HidetoNiwa/one-person-catch-robo/CAD/ロボット/Images/ロボット.iam 構造解析レポート 2020_07_17/0/Constraint_0_1.png

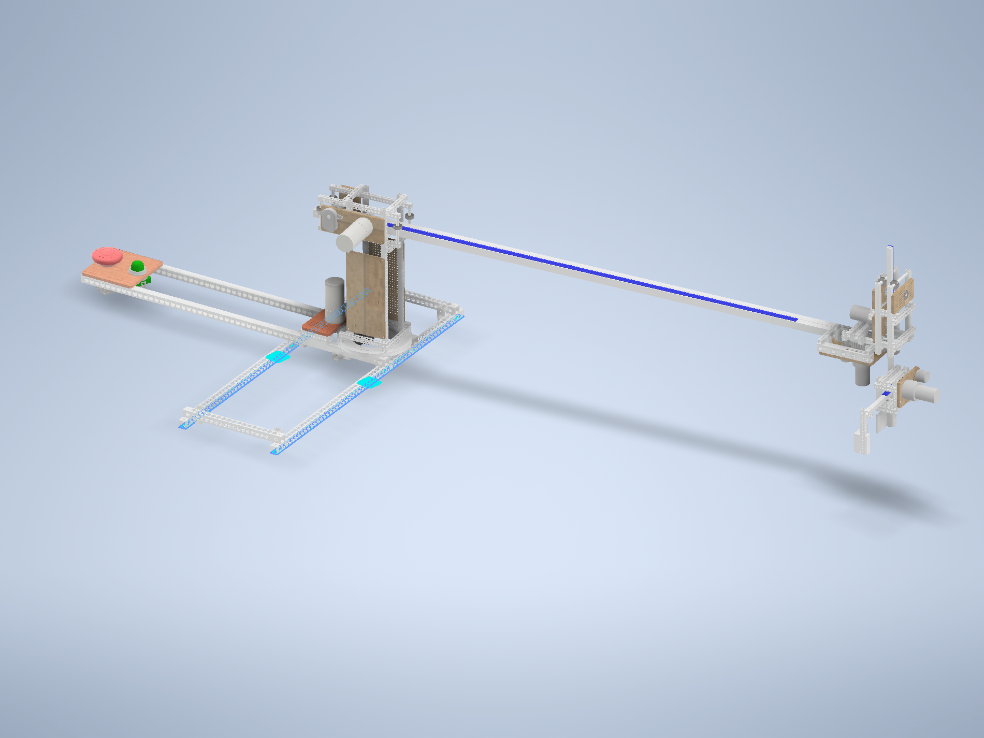
CAD/ロボット/Images/ロボット.iam 構造解析レポート 2020_07_17/0/Constraint_0_1.png
