HidetoNiwa/one-person-catch-robo/CAD/ロボット/ハンド/ハンド.png

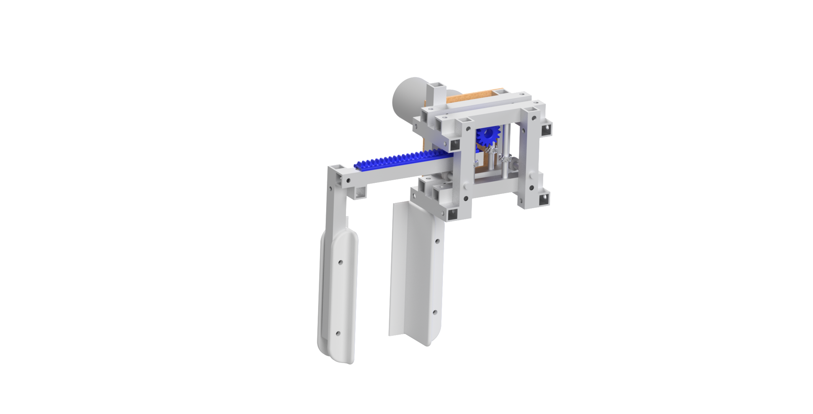
CAD/ロボット/ハンド/ハンド.png
