HidetoNiwa/one-person-catch-robo/CAD/ロボット/画像/ハンド2.png

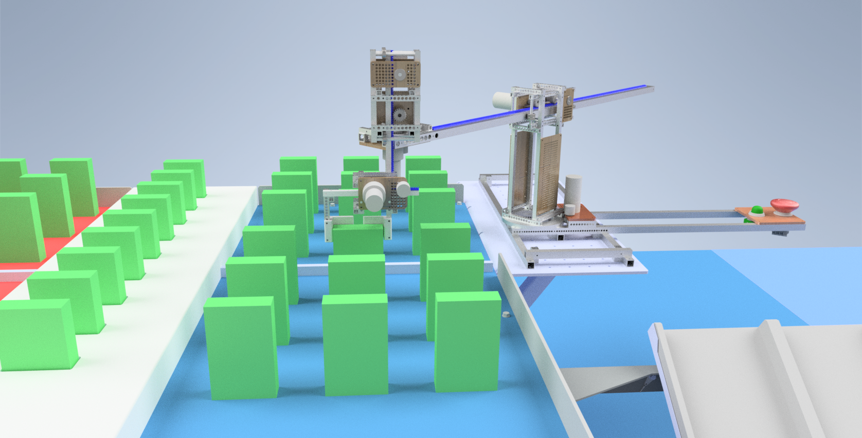
CAD/ロボット/画像/ハンド2.png
