HidetoNiwa/one-person-catch-robo/CAD/ロボット/画像/ハンド.png

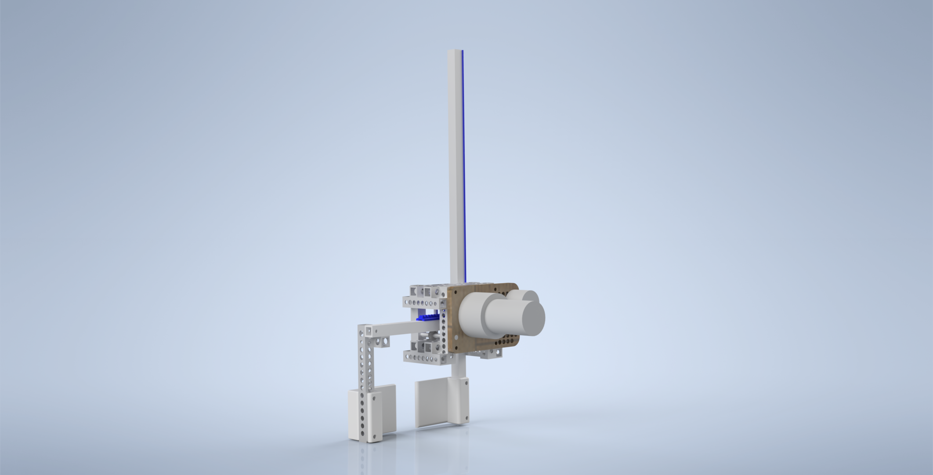
CAD/ロボット/画像/ハンド.png
