HidetoNiwa/one-person-catch-robo/CAD/ロボット/画像/ロボット2.png

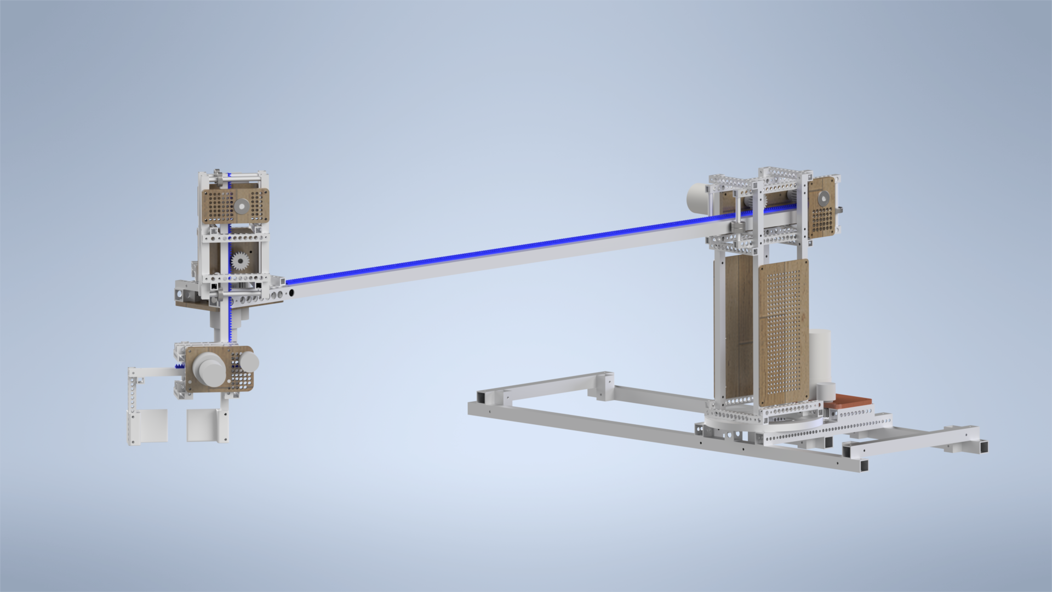
CAD/ロボット/画像/ロボット2.png
