HidetoNiwa/one-person-catch-robo/CAD/ロボット/画像/ロボット3.png

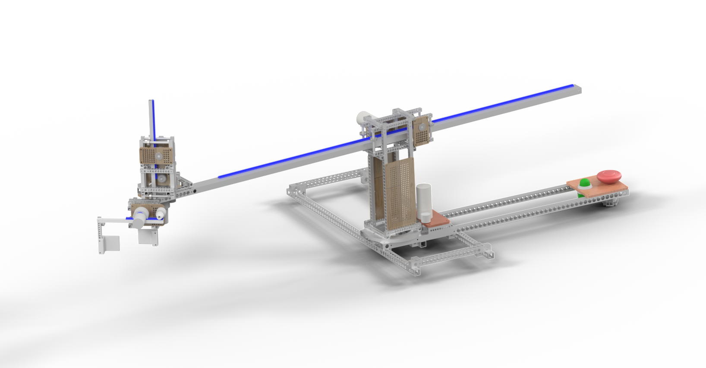
CAD/ロボット/画像/ロボット3.png
