HidetoNiwa/one-person-catch-robo/CAD/ロボット/画像/ロボット.bmp

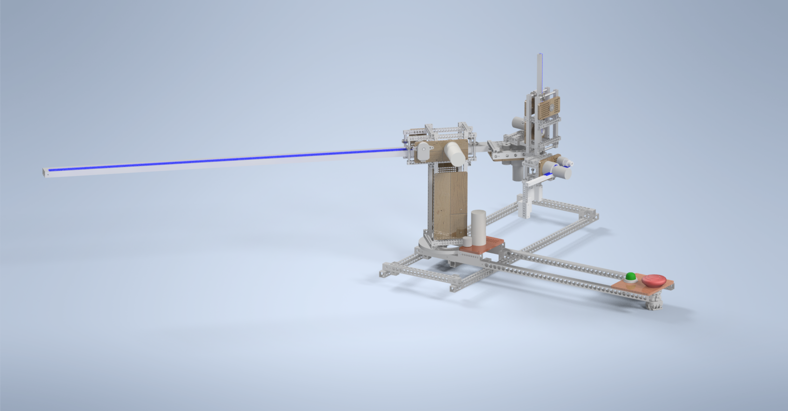
CAD/ロボット/画像/ロボット.bmp
