HidetoNiwa/one-person-catch-robo/CAD/ロボット/画像/ロボット.png

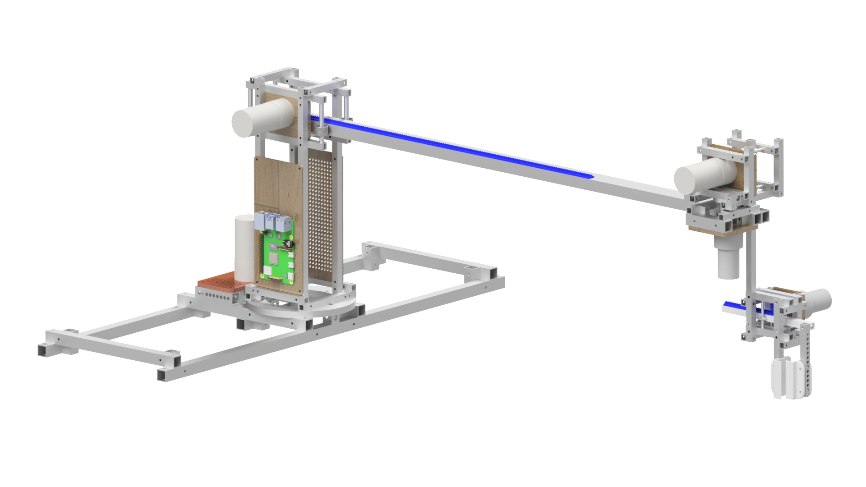
CAD/ロボット/画像/ロボット.png
