HidetoNiwa/one-person-catch-robo/CAD/ロボット/画像/全体.png

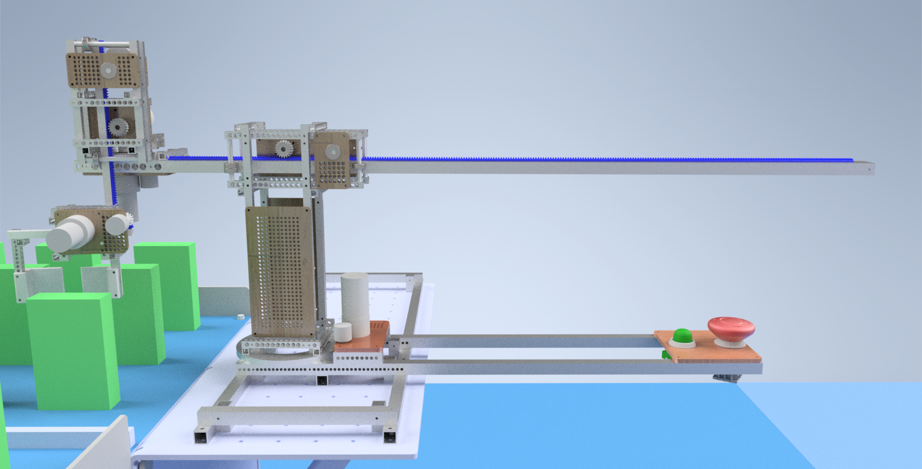
CAD/ロボット/画像/全体.png
