HidetoNiwa/one-person-catch-robo/YOLO/bisco/back_001.jpg

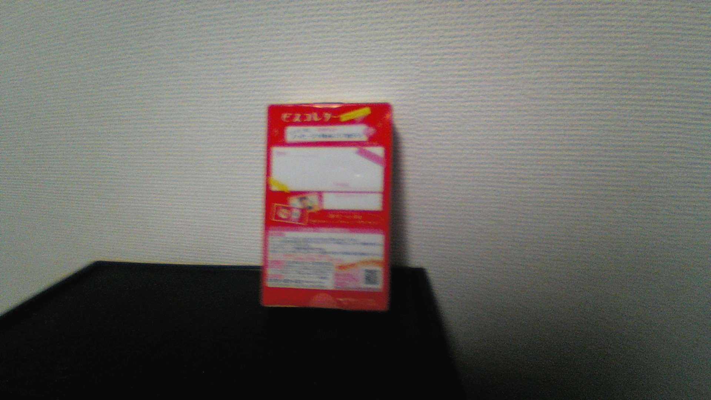
YOLO/bisco/back_001.jpg
