HidetoNiwa/one-person-catch-robo/YOLO/bisco/back_002.jpg

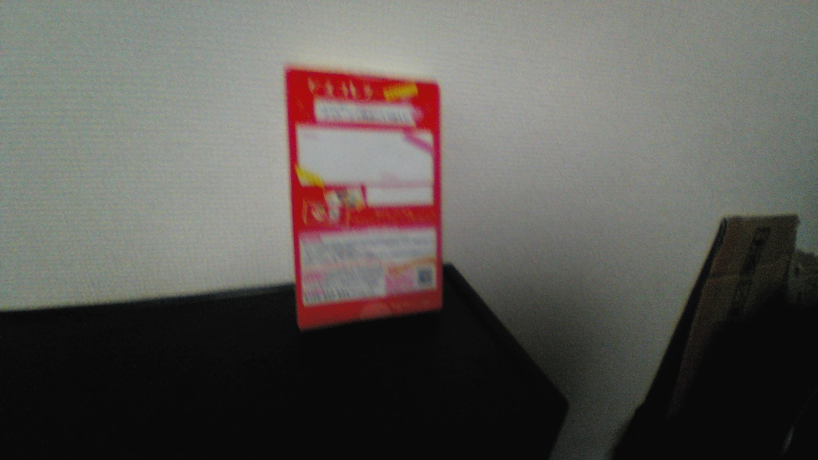
YOLO/bisco/back_002.jpg
