HidetoNiwa/one-person-catch-robo/YOLO/bisco/back_003.jpg

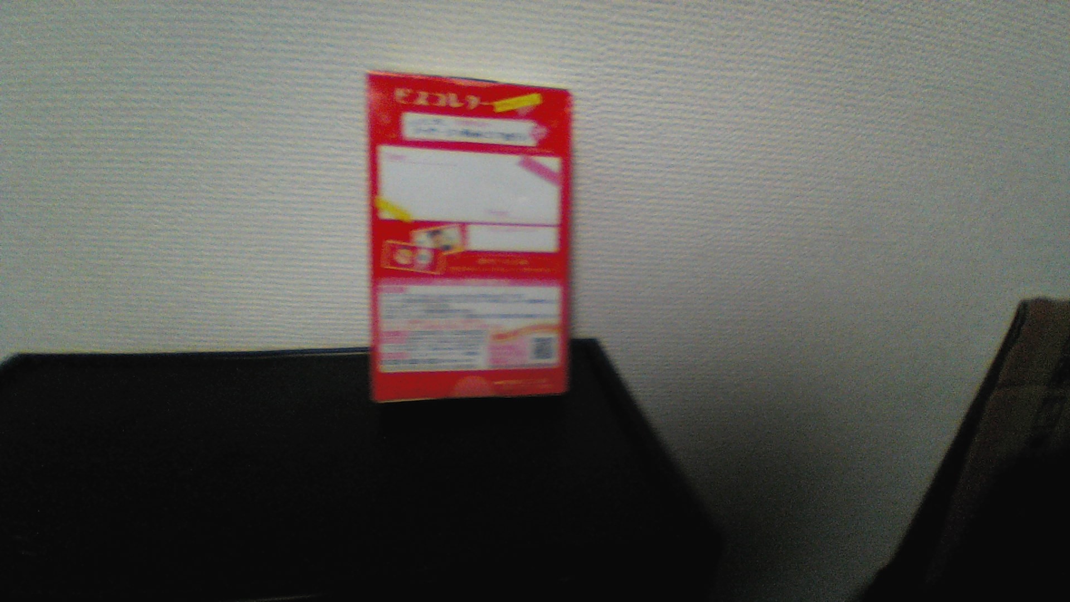
YOLO/bisco/back_003.jpg
