HidetoNiwa/one-person-catch-robo/YOLO/bisco/back_004.jpg

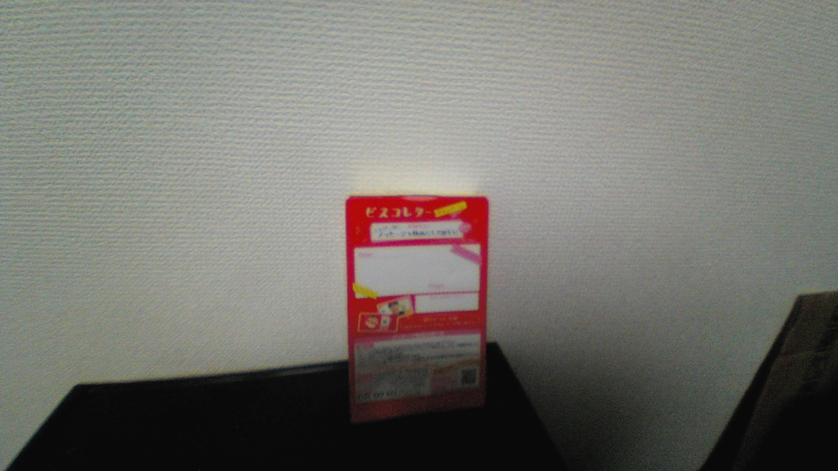
YOLO/bisco/back_004.jpg
