HidetoNiwa/one-person-catch-robo/YOLO/bisco/back_005.jpg

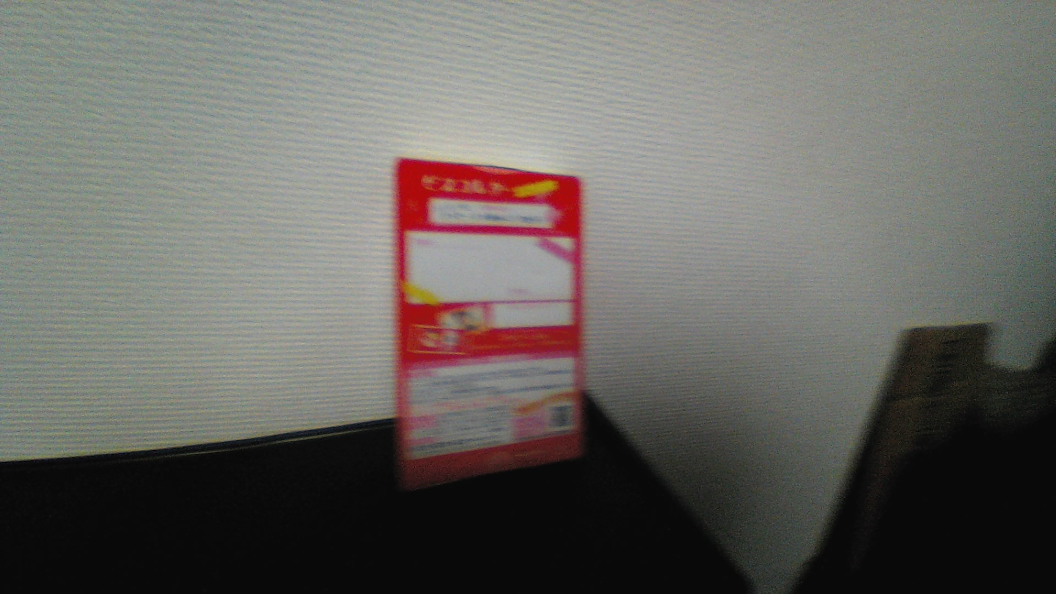
YOLO/bisco/back_005.jpg
