HidetoNiwa/one-person-catch-robo/YOLO/bisco/back_006.jpg

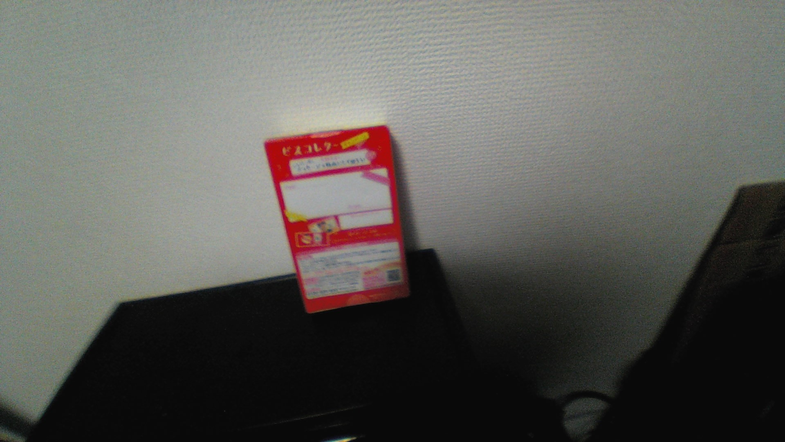
YOLO/bisco/back_006.jpg
