HidetoNiwa/one-person-catch-robo/YOLO/bisco/back_007.jpg

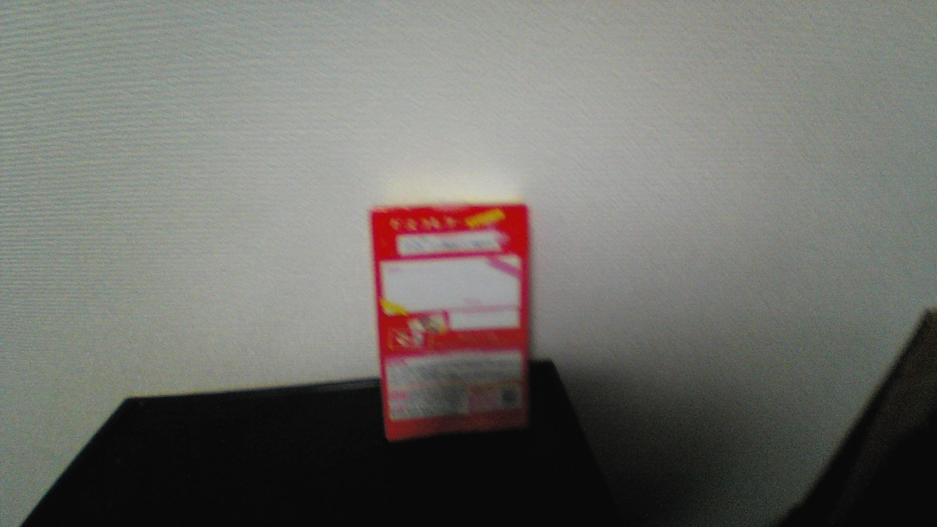
YOLO/bisco/back_007.jpg
