HidetoNiwa/one-person-catch-robo/YOLO/bisco/back_008.jpg

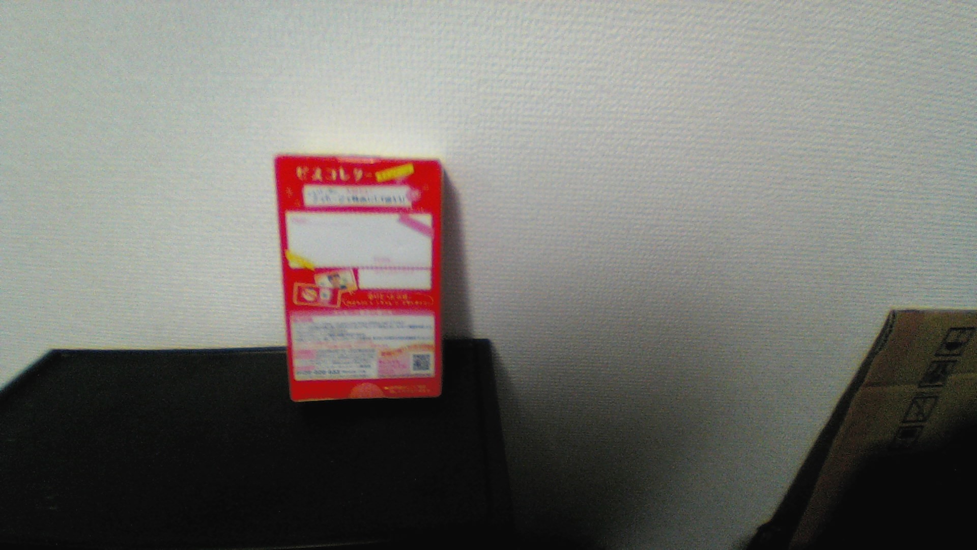
YOLO/bisco/back_008.jpg
