HidetoNiwa/one-person-catch-robo/YOLO/bisco/back_009.jpg

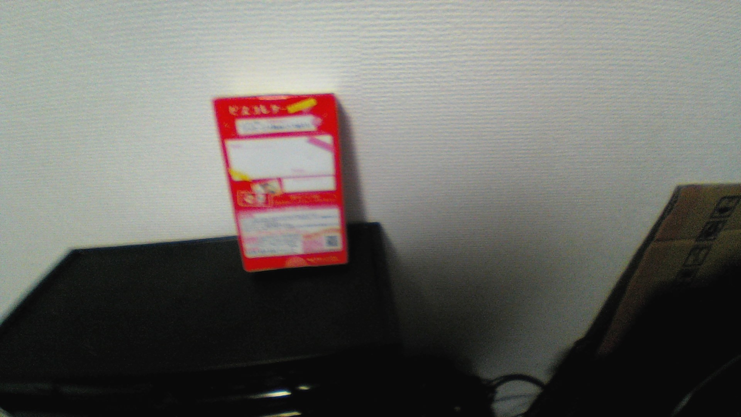
YOLO/bisco/back_009.jpg
