HidetoNiwa/one-person-catch-robo/YOLO/bisco/back_010.jpg

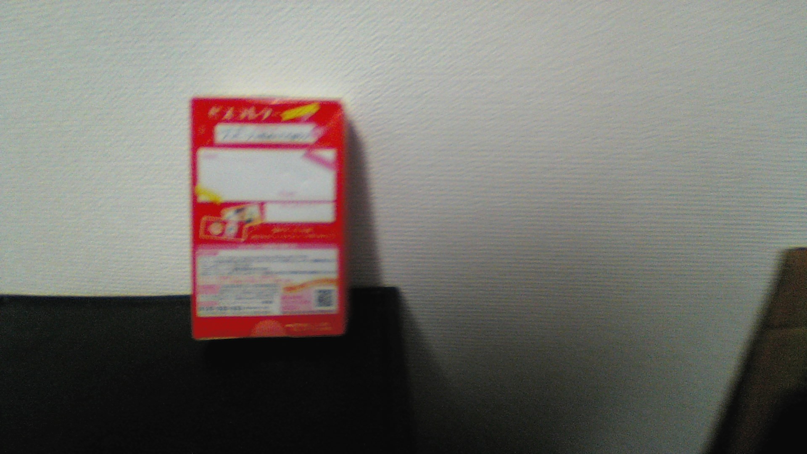
YOLO/bisco/back_010.jpg
