HidetoNiwa/one-person-catch-robo/YOLO/bisco/back_011.jpg

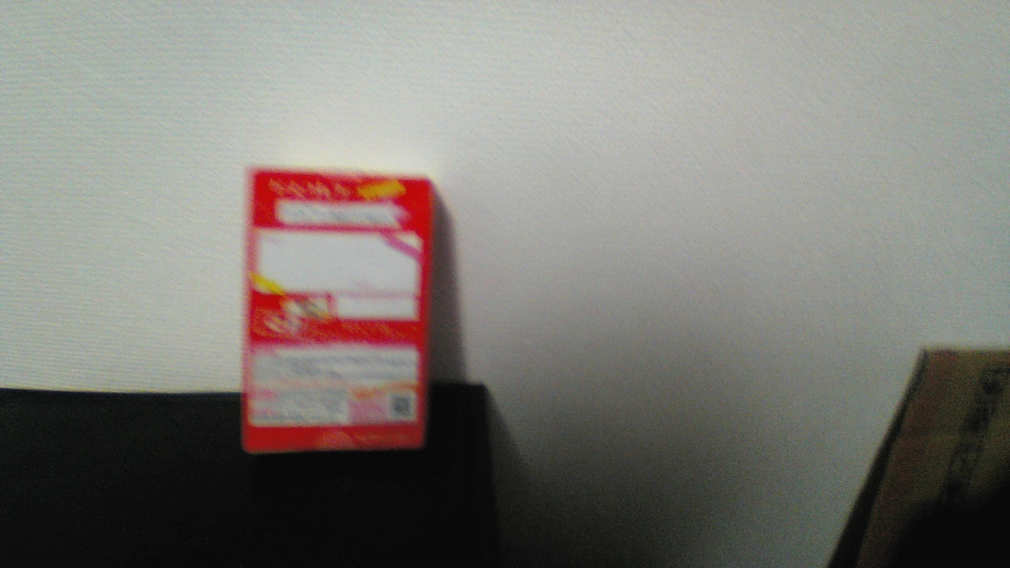
YOLO/bisco/back_011.jpg
