HidetoNiwa/one-person-catch-robo/YOLO/bisco/back_012.jpg

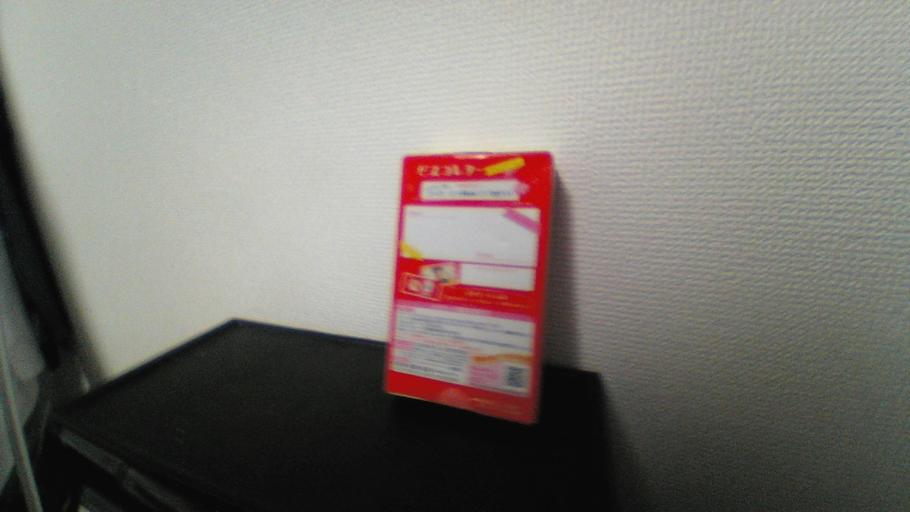
YOLO/bisco/back_012.jpg
