HidetoNiwa/one-person-catch-robo/YOLO/bisco/back_013.jpg

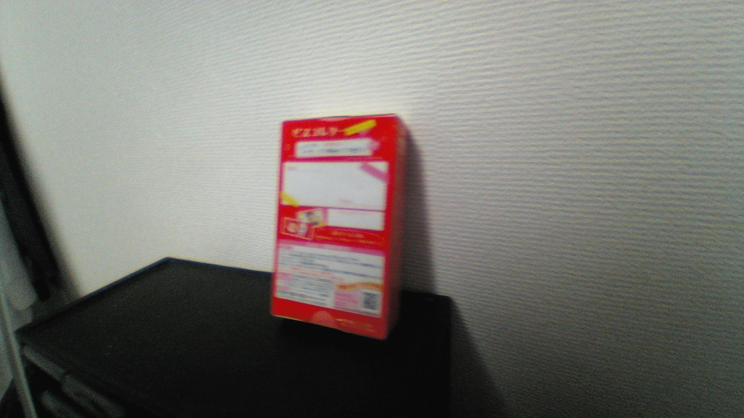
YOLO/bisco/back_013.jpg
