HidetoNiwa/one-person-catch-robo/YOLO/bisco/back_014.jpg

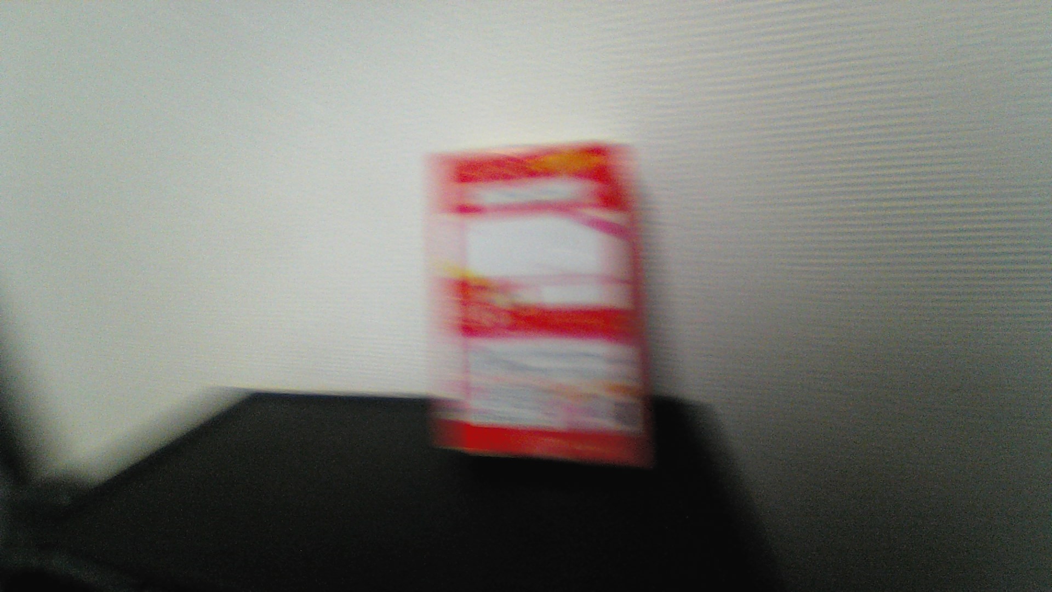
YOLO/bisco/back_014.jpg
