HidetoNiwa/one-person-catch-robo/YOLO/bisco/back_015.jpg

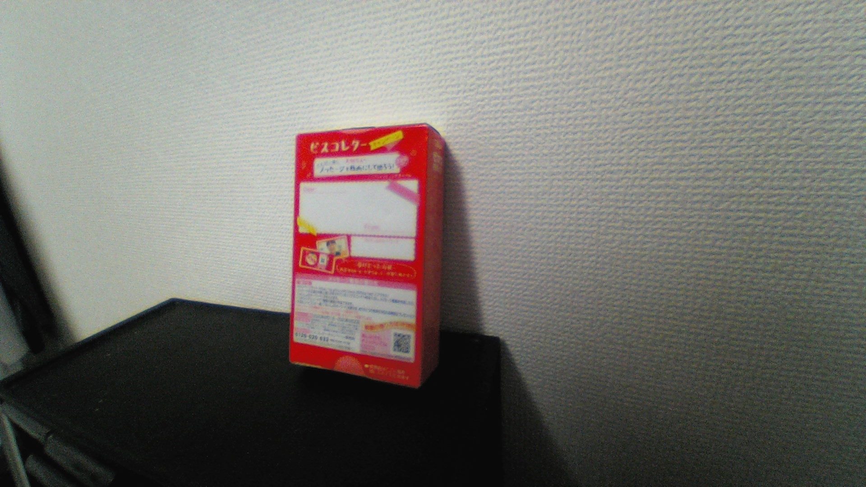
YOLO/bisco/back_015.jpg
