HidetoNiwa/one-person-catch-robo/YOLO/bisco/back_016.jpg

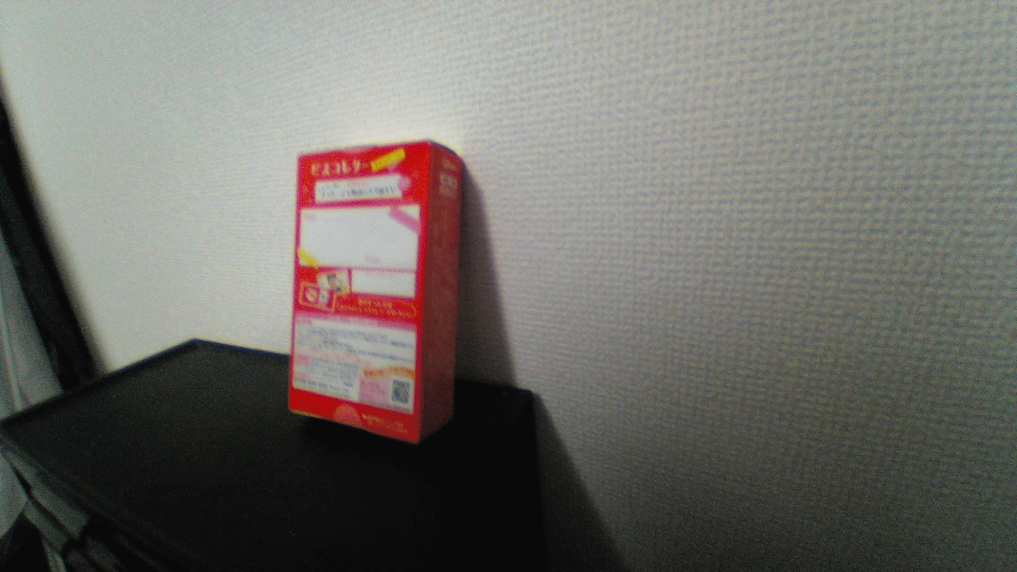
YOLO/bisco/back_016.jpg
