HidetoNiwa/one-person-catch-robo/YOLO/bisco/back_017.jpg

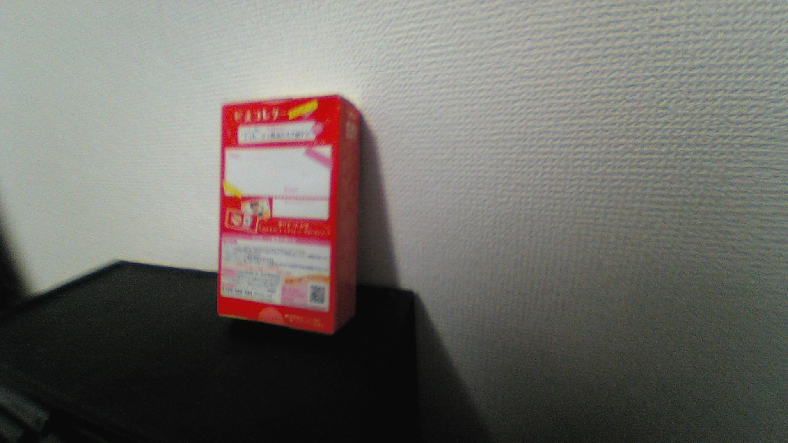
YOLO/bisco/back_017.jpg
