HidetoNiwa/one-person-catch-robo/YOLO/bisco/back_018.jpg

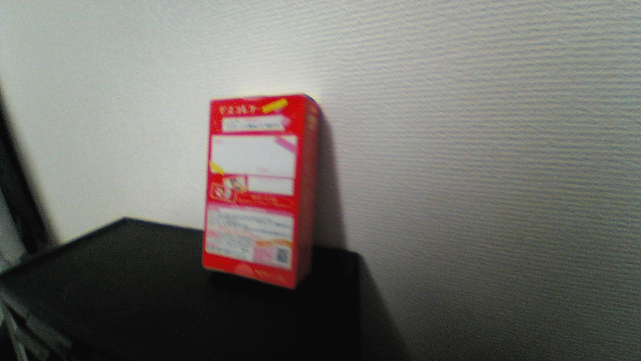
YOLO/bisco/back_018.jpg
