HidetoNiwa/one-person-catch-robo/YOLO/bisco/back_019.jpg

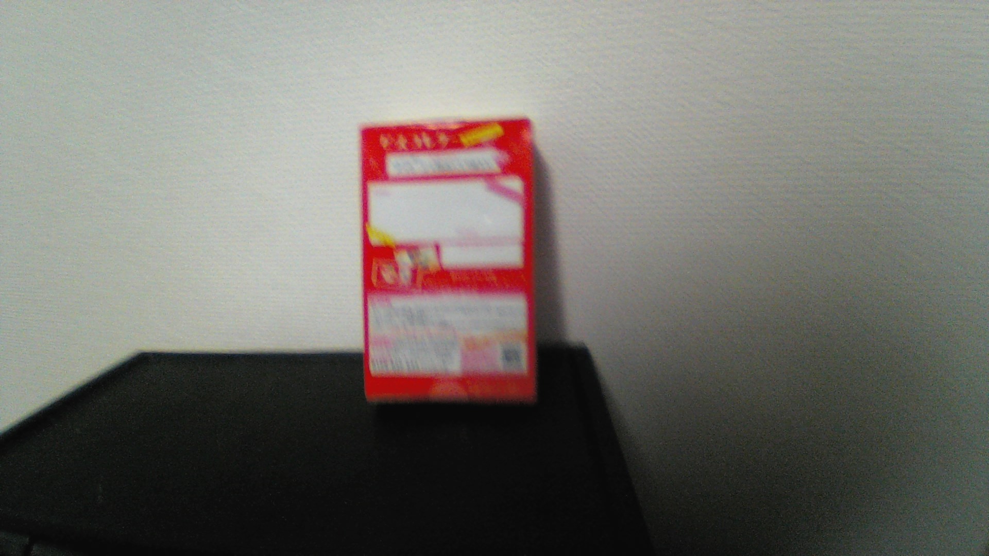
YOLO/bisco/back_019.jpg
