HidetoNiwa/one-person-catch-robo/YOLO/bisco/back_021.jpg

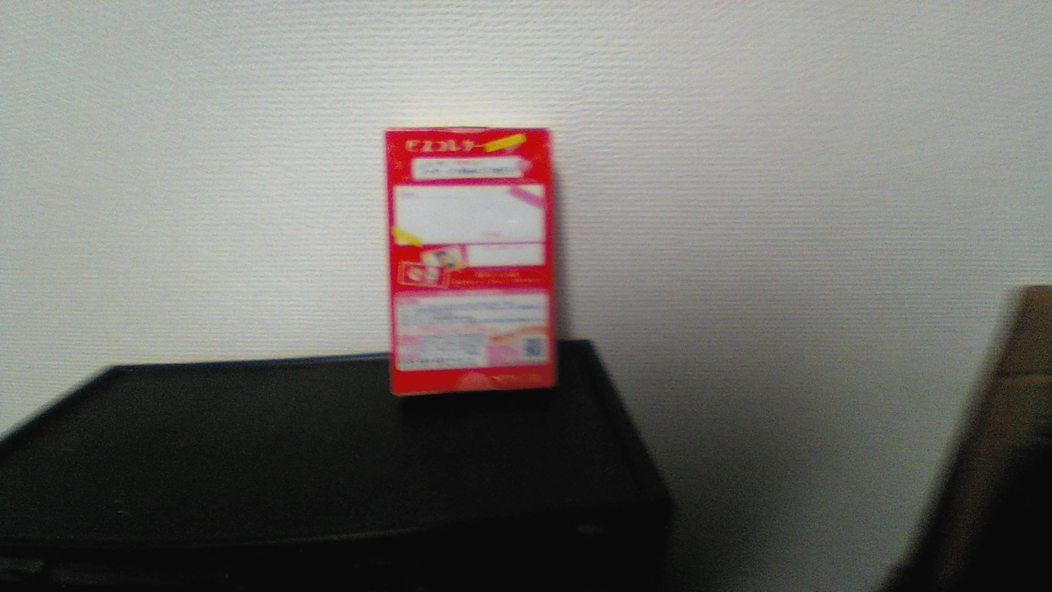
YOLO/bisco/back_021.jpg
