HidetoNiwa/one-person-catch-robo/YOLO/bisco/back_022.jpg

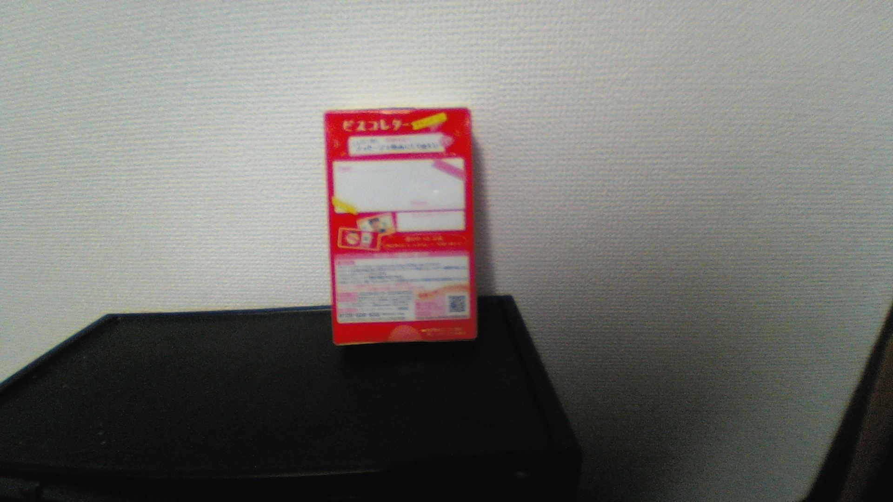
YOLO/bisco/back_022.jpg
