HidetoNiwa/one-person-catch-robo/YOLO/bisco/back_023.jpg

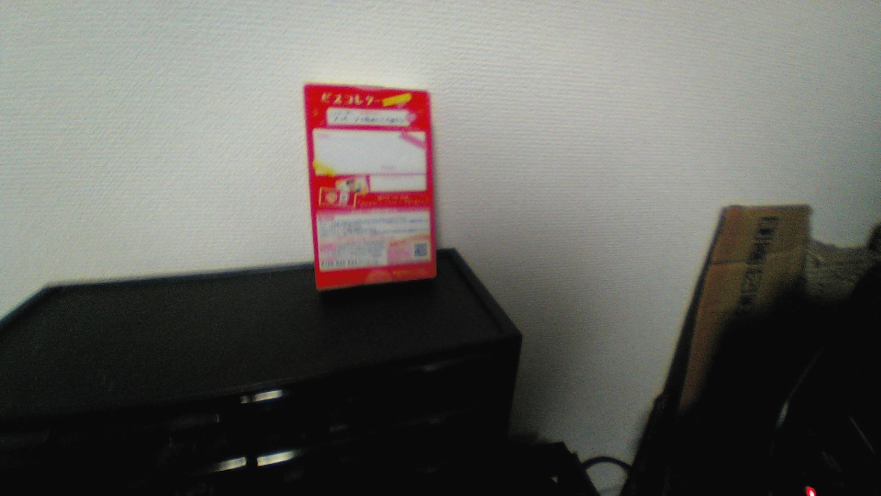
YOLO/bisco/back_023.jpg
