HidetoNiwa/one-person-catch-robo/YOLO/bisco/back_024.jpg

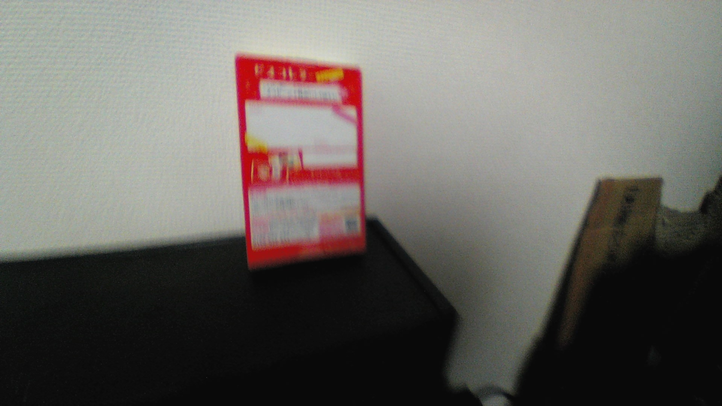
YOLO/bisco/back_024.jpg
