HidetoNiwa/one-person-catch-robo/YOLO/bisco/back_026.jpg

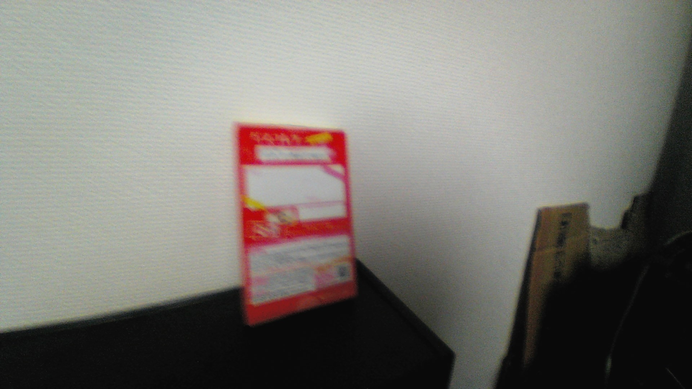
YOLO/bisco/back_026.jpg
