HidetoNiwa/one-person-catch-robo/YOLO/bisco/back_027.jpg

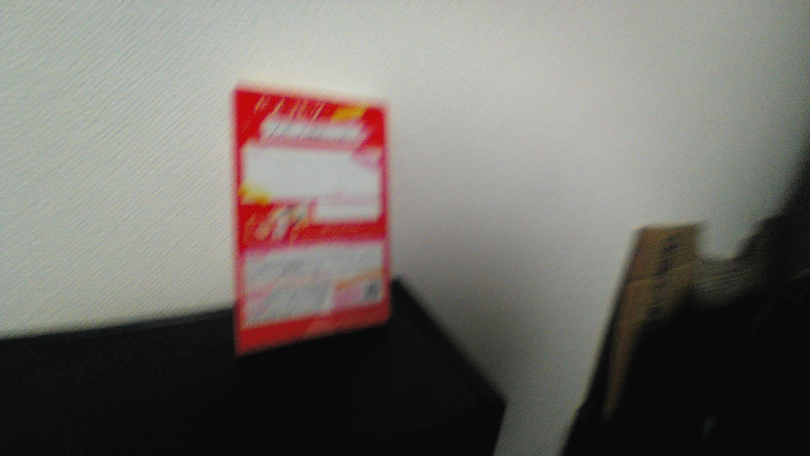
YOLO/bisco/back_027.jpg
