HidetoNiwa/one-person-catch-robo/YOLO/bisco/back_028.jpg

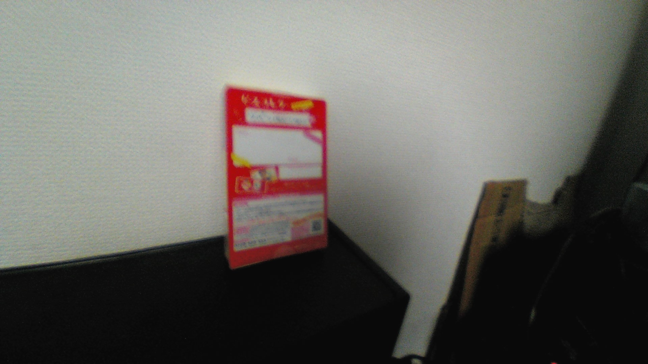
YOLO/bisco/back_028.jpg
