HidetoNiwa/one-person-catch-robo/YOLO/bisco/back_029.jpg

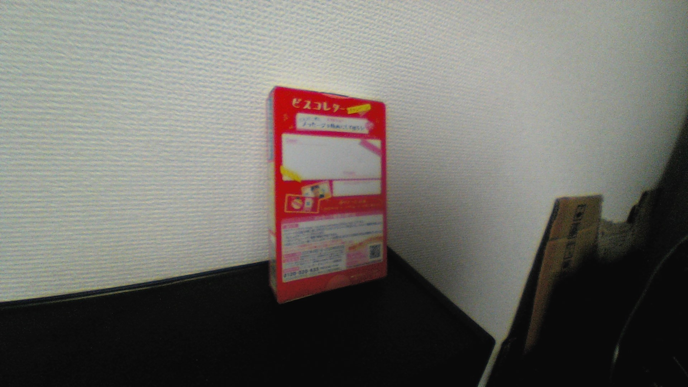
YOLO/bisco/back_029.jpg
