HidetoNiwa/one-person-catch-robo/YOLO/bisco/back_030.jpg

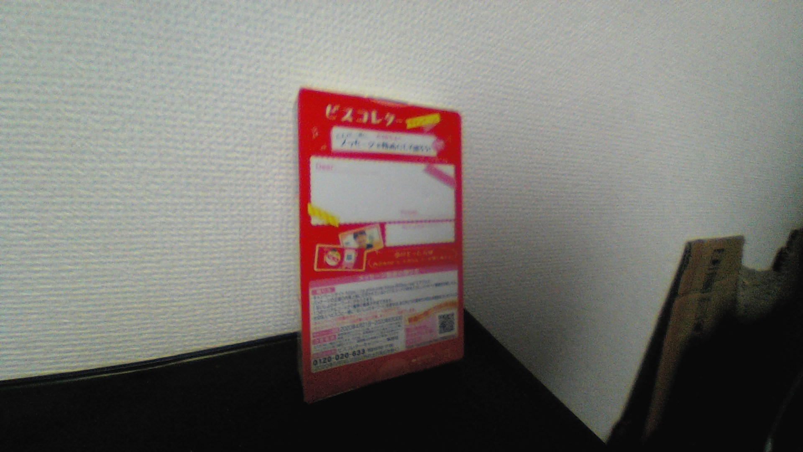
YOLO/bisco/back_030.jpg
