HidetoNiwa/one-person-catch-robo/YOLO/bisco/back_031.jpg

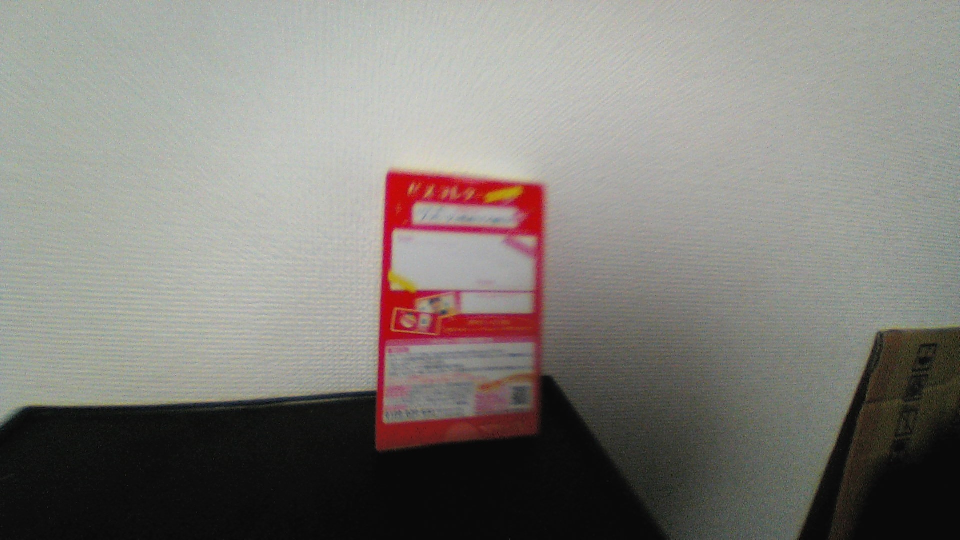
YOLO/bisco/back_031.jpg
