HidetoNiwa/one-person-catch-robo/YOLO/bisco/back_032.jpg

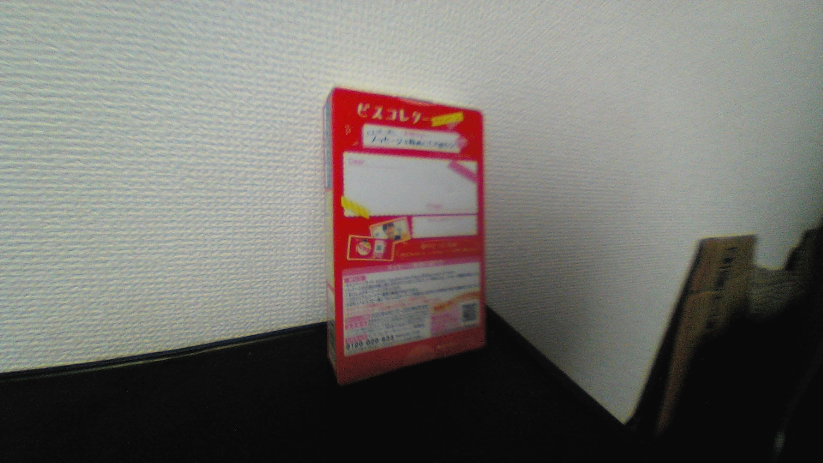
YOLO/bisco/back_032.jpg
