HidetoNiwa/one-person-catch-robo/YOLO/bisco/back_033.jpg

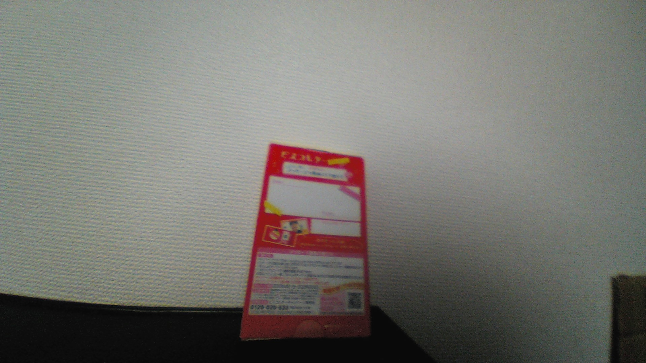
YOLO/bisco/back_033.jpg
