HidetoNiwa/one-person-catch-robo/YOLO/bisco/back_034.jpg

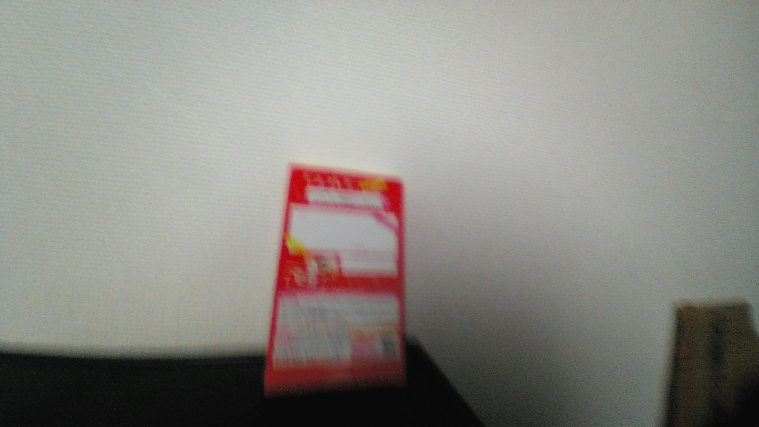
YOLO/bisco/back_034.jpg
