HidetoNiwa/one-person-catch-robo/YOLO/bisco/back_035.jpg

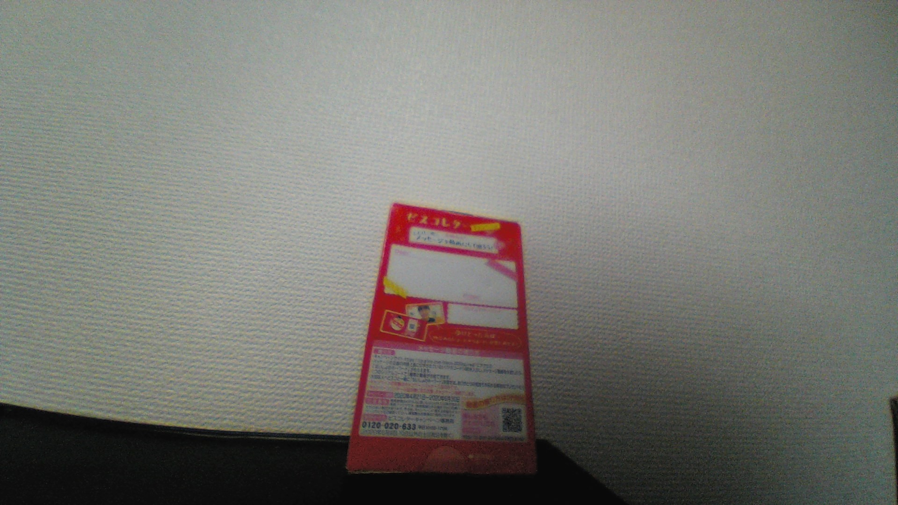
YOLO/bisco/back_035.jpg
