HidetoNiwa/one-person-catch-robo/YOLO/bisco/back_037.jpg

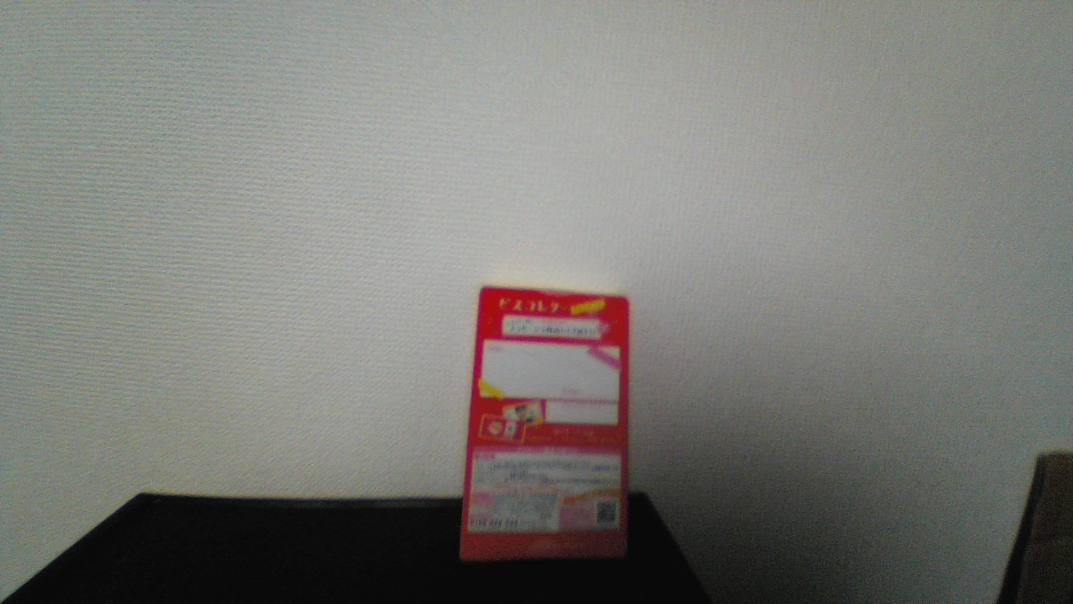
YOLO/bisco/back_037.jpg
