HidetoNiwa/one-person-catch-robo/YOLO/bisco/back_038.jpg

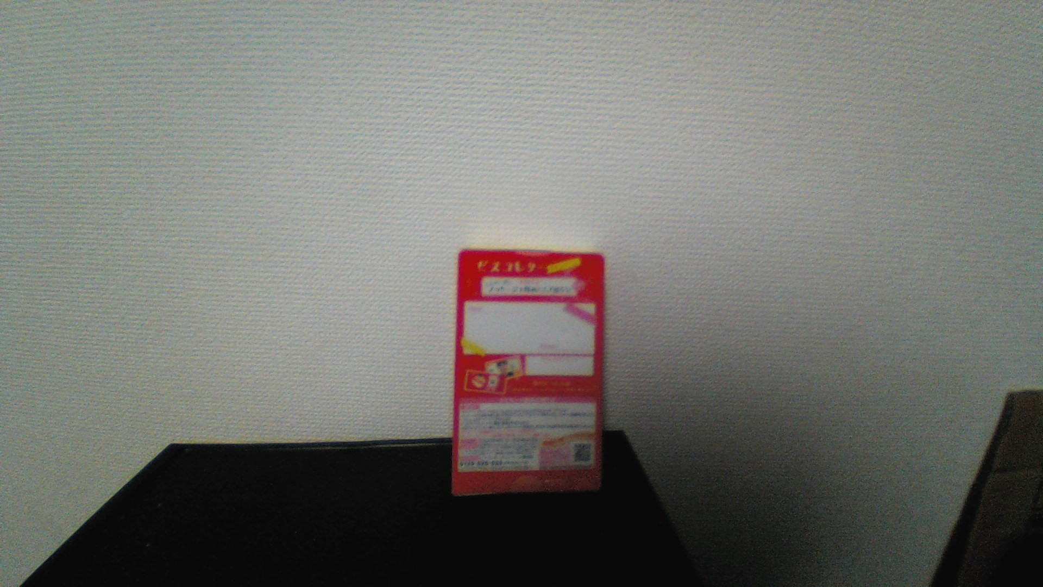
YOLO/bisco/back_038.jpg
