HidetoNiwa/one-person-catch-robo/YOLO/bisco/back_039.jpg

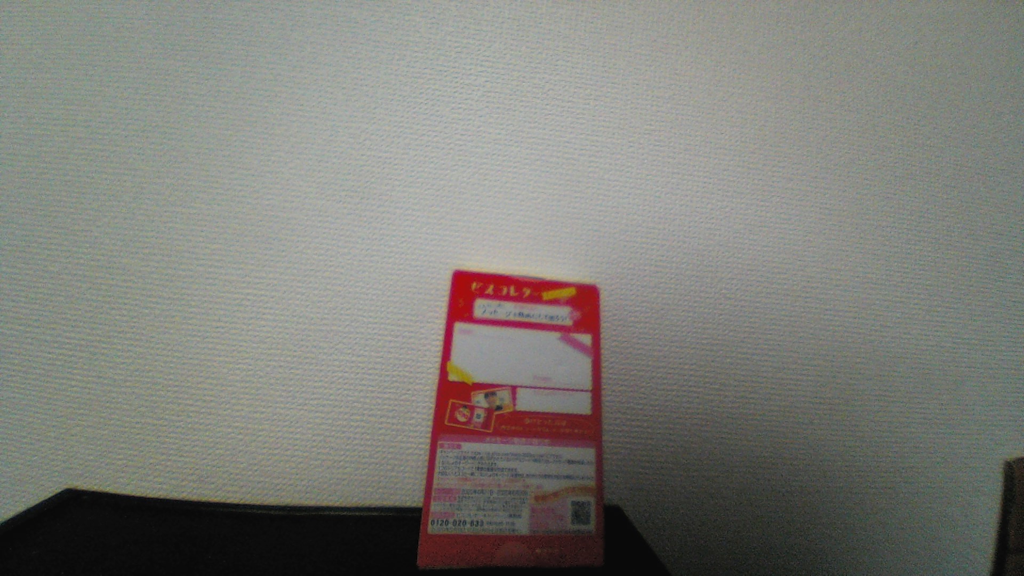
YOLO/bisco/back_039.jpg
