HidetoNiwa/one-person-catch-robo/YOLO/bisco/back_040.jpg

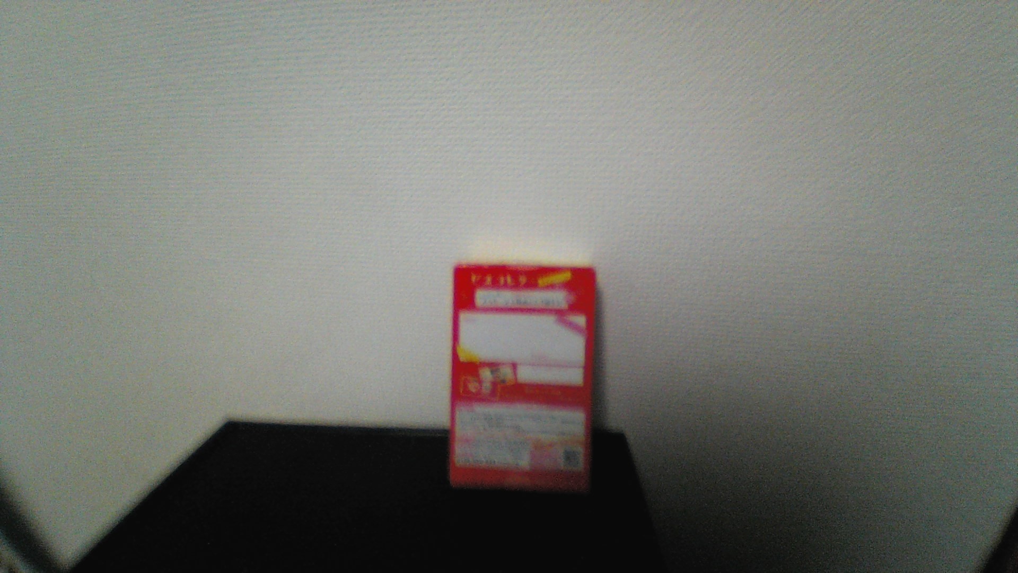
YOLO/bisco/back_040.jpg
