HidetoNiwa/one-person-catch-robo/YOLO/bisco/back_042.jpg

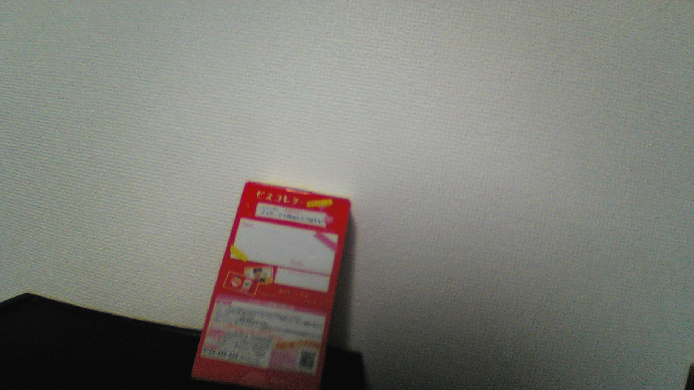
YOLO/bisco/back_042.jpg
