HidetoNiwa/one-person-catch-robo/YOLO/bisco/back_043.jpg

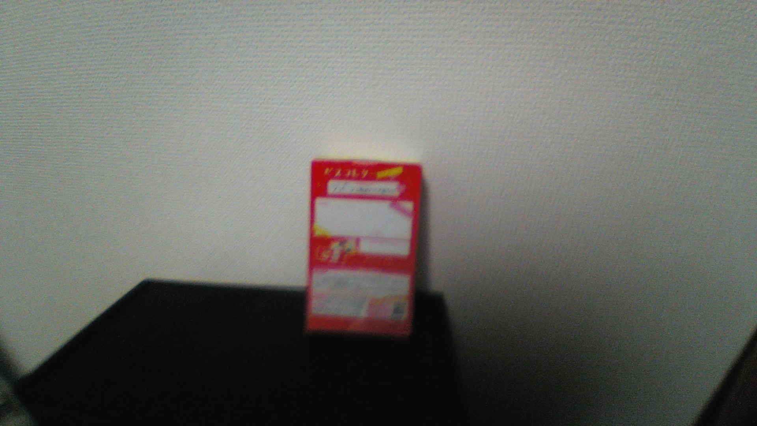
YOLO/bisco/back_043.jpg
