HidetoNiwa/one-person-catch-robo/YOLO/bisco/back_044.jpg

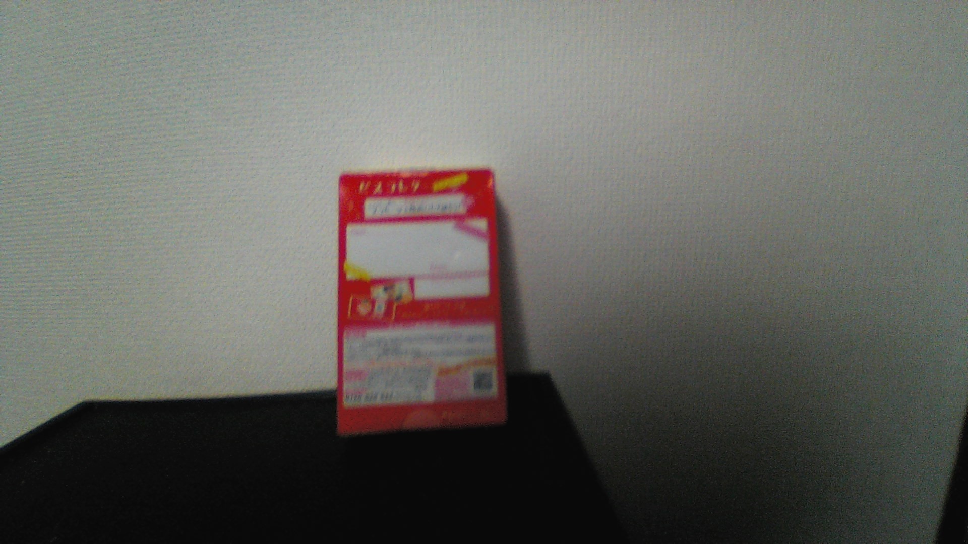
YOLO/bisco/back_044.jpg
