HidetoNiwa/one-person-catch-robo/YOLO/bisco/back_045.jpg

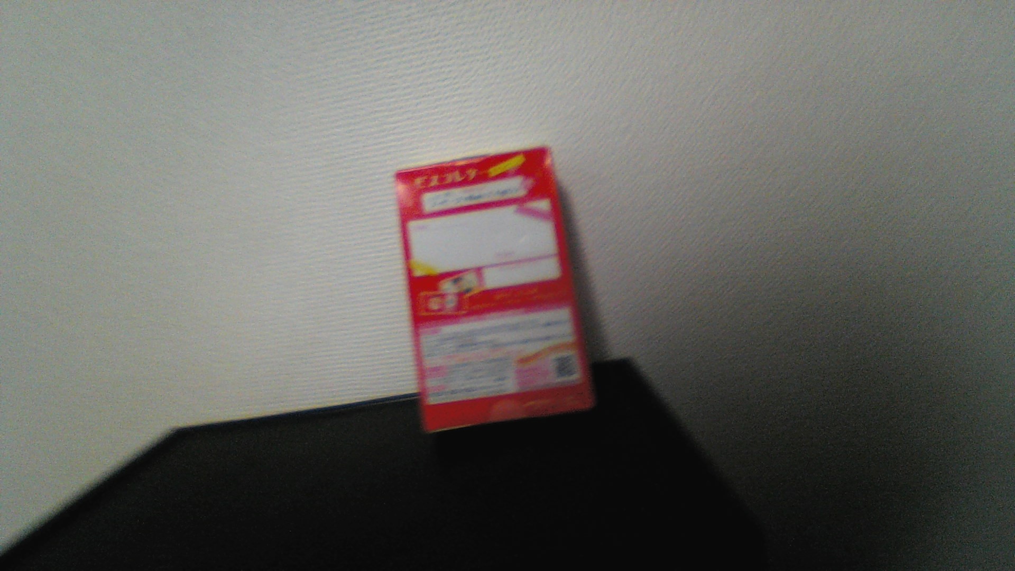
YOLO/bisco/back_045.jpg
