HidetoNiwa/one-person-catch-robo/YOLO/bisco/back_046.jpg

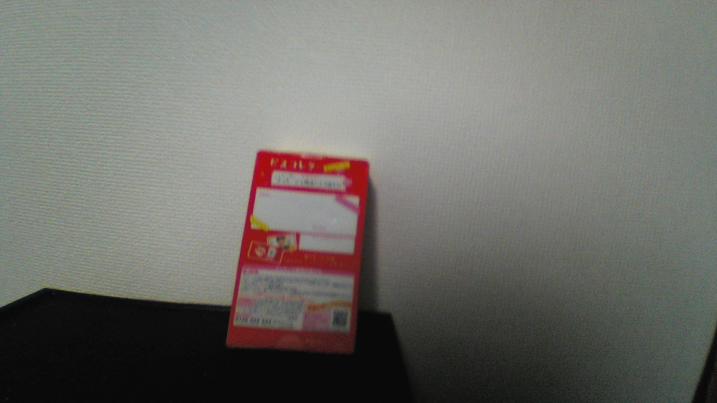
YOLO/bisco/back_046.jpg
