HidetoNiwa/one-person-catch-robo/YOLO/bisco/back_047.jpg

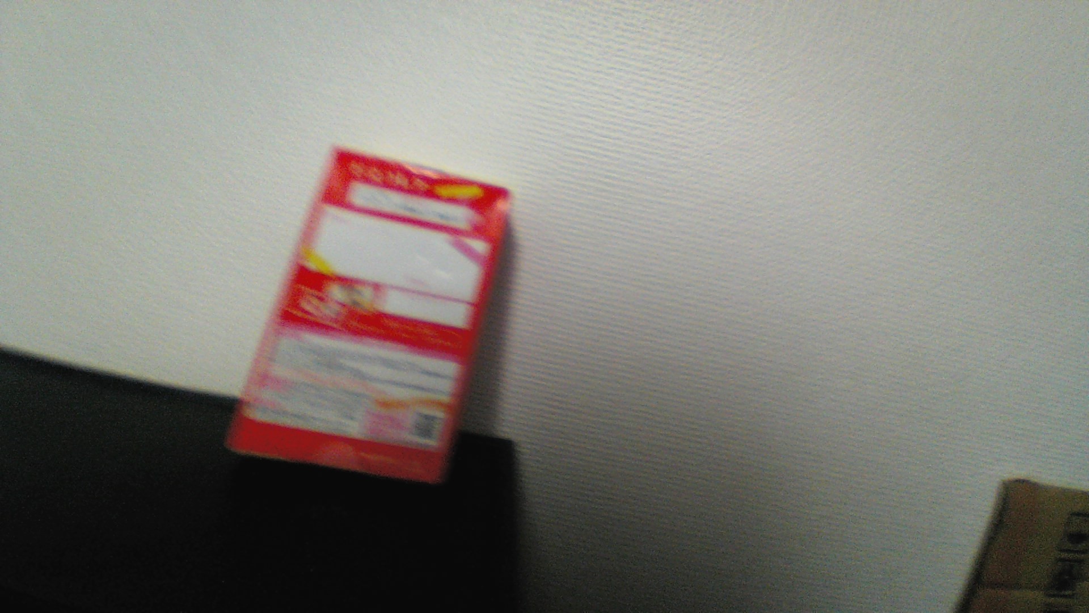
YOLO/bisco/back_047.jpg
