HidetoNiwa/one-person-catch-robo/YOLO/bisco/back_048.jpg

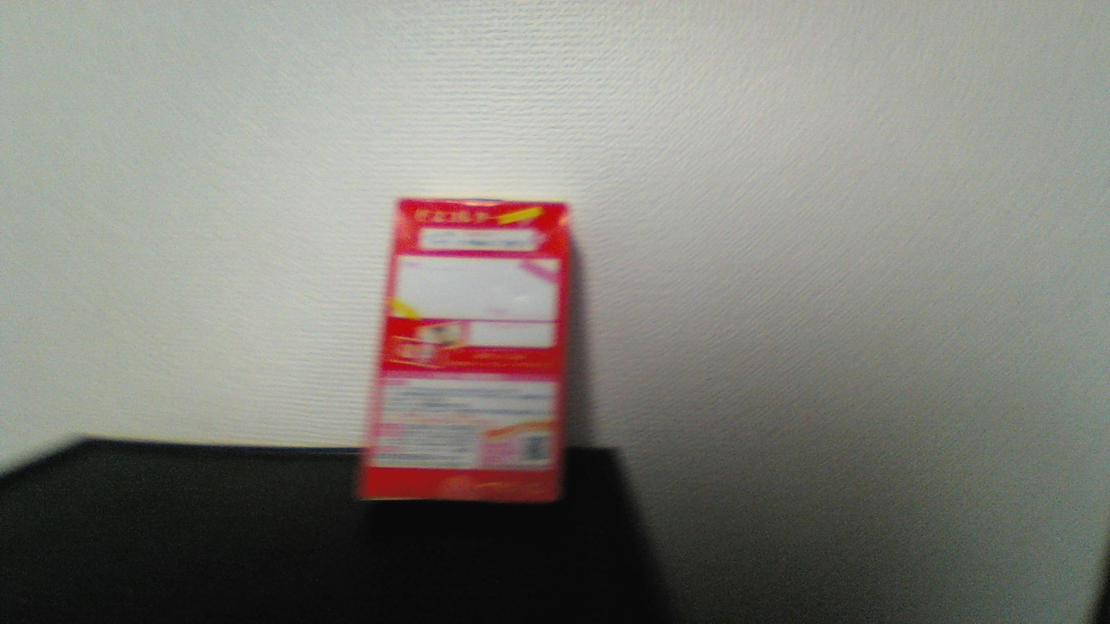
YOLO/bisco/back_048.jpg
