HidetoNiwa/one-person-catch-robo/YOLO/bisco/back_049.jpg

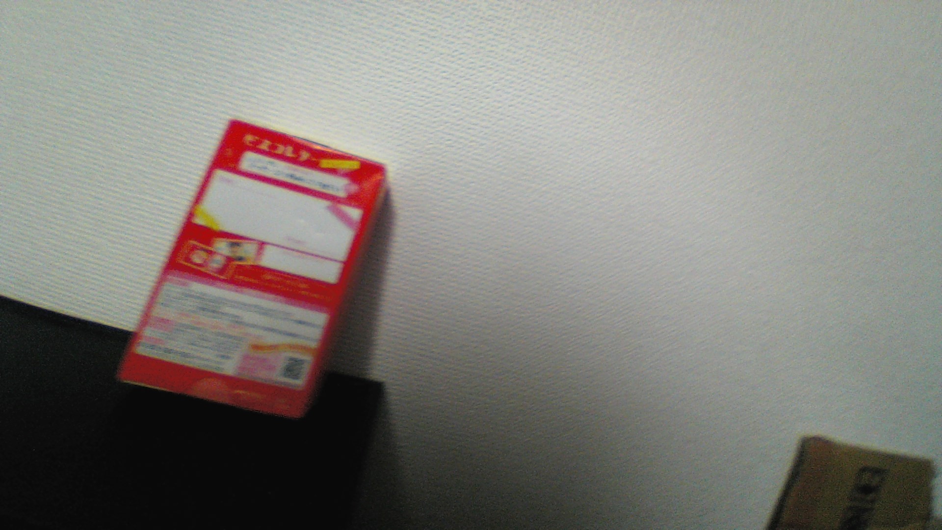
YOLO/bisco/back_049.jpg
