HidetoNiwa/one-person-catch-robo/YOLO/bisco/back_050.jpg

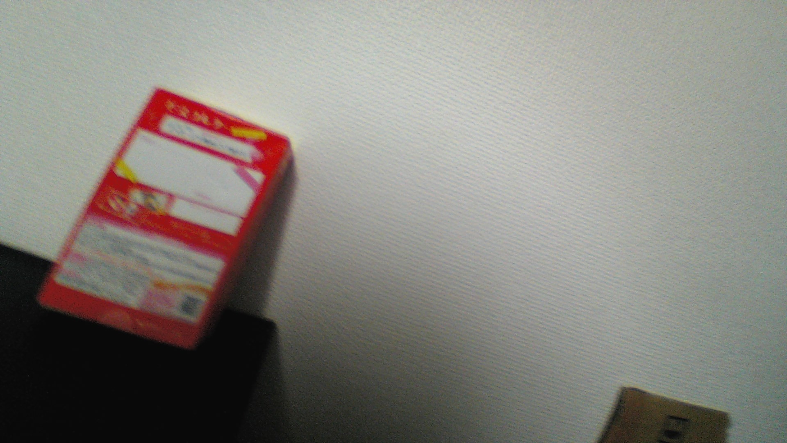
YOLO/bisco/back_050.jpg
