HidetoNiwa/one-person-catch-robo/YOLO/bisco/back_051.jpg

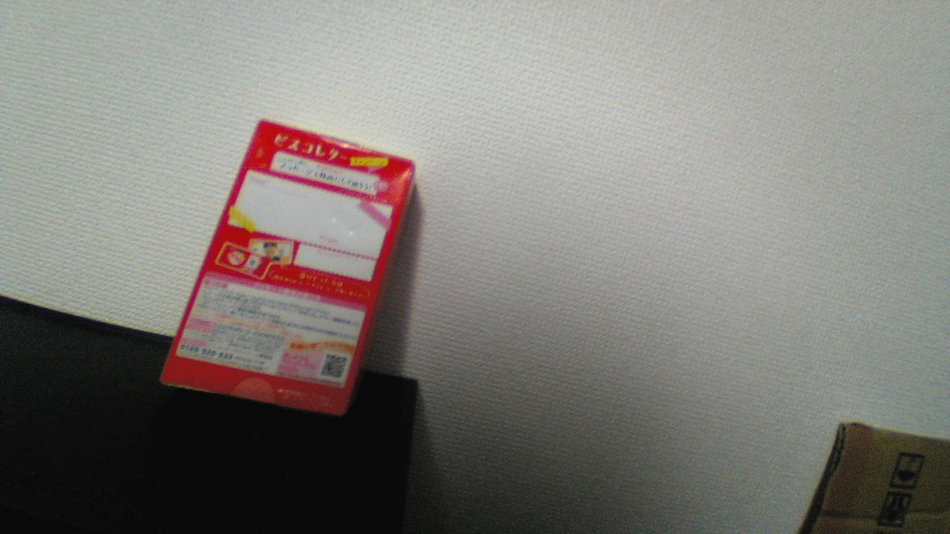
YOLO/bisco/back_051.jpg
