HidetoNiwa/one-person-catch-robo/YOLO/bisco/back_052.jpg

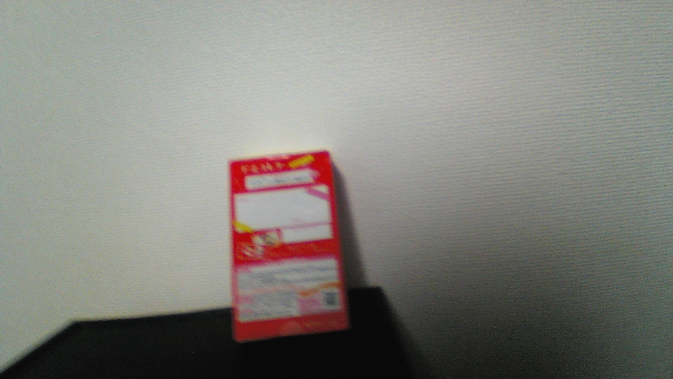
YOLO/bisco/back_052.jpg
