HidetoNiwa/one-person-catch-robo/YOLO/bisco/back_053.jpg

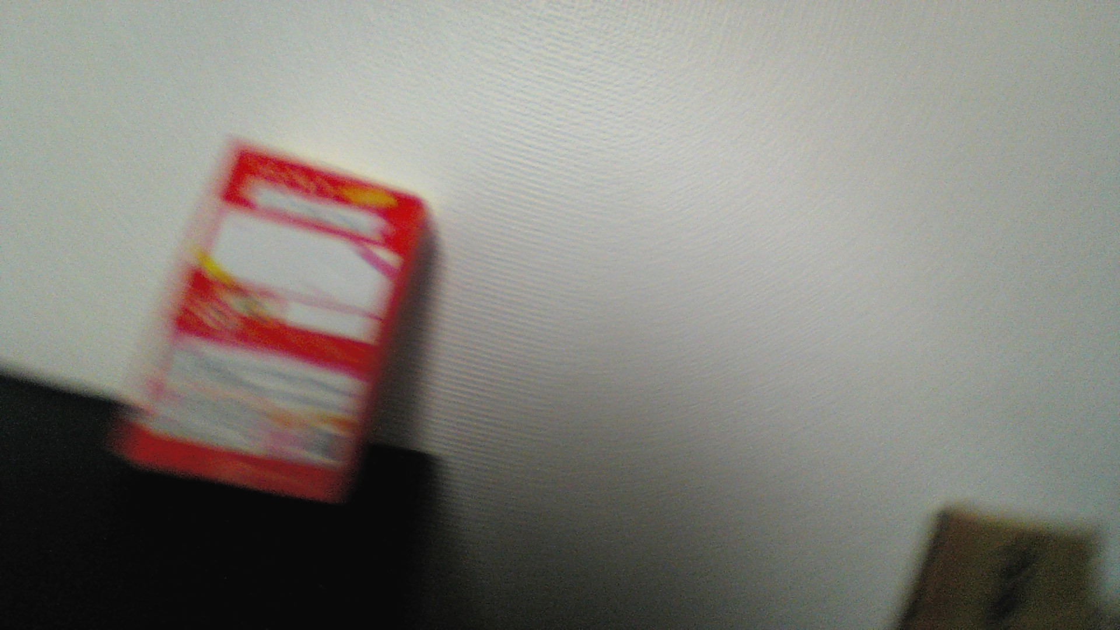
YOLO/bisco/back_053.jpg
