HidetoNiwa/one-person-catch-robo/YOLO/bisco/back_054.jpg

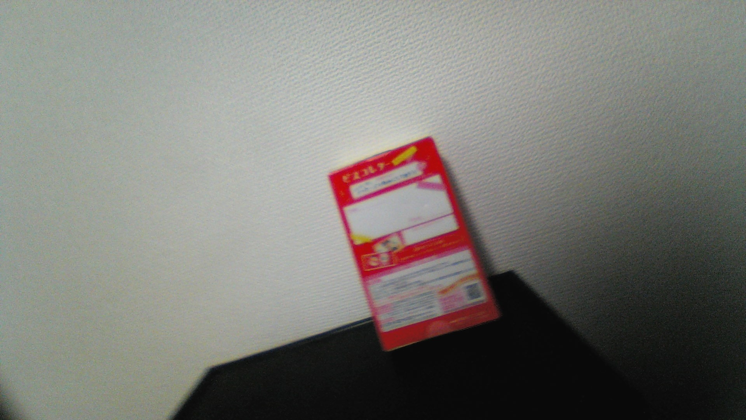
YOLO/bisco/back_054.jpg
