HidetoNiwa/one-person-catch-robo/YOLO/bisco/back_055.jpg

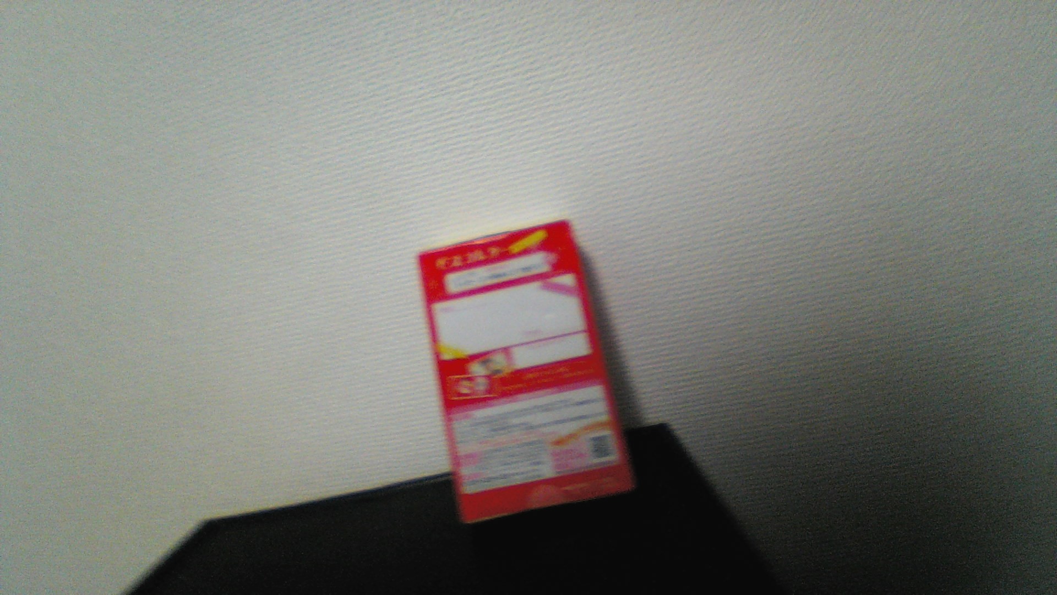
YOLO/bisco/back_055.jpg
