HidetoNiwa/one-person-catch-robo/YOLO/bisco/back_056.jpg

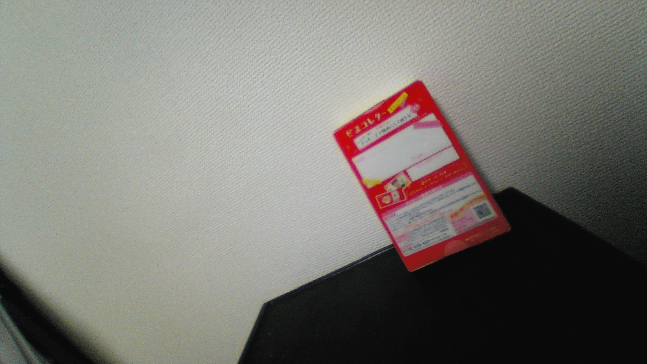
YOLO/bisco/back_056.jpg
