HidetoNiwa/one-person-catch-robo/YOLO/bisco/face_001.jpg

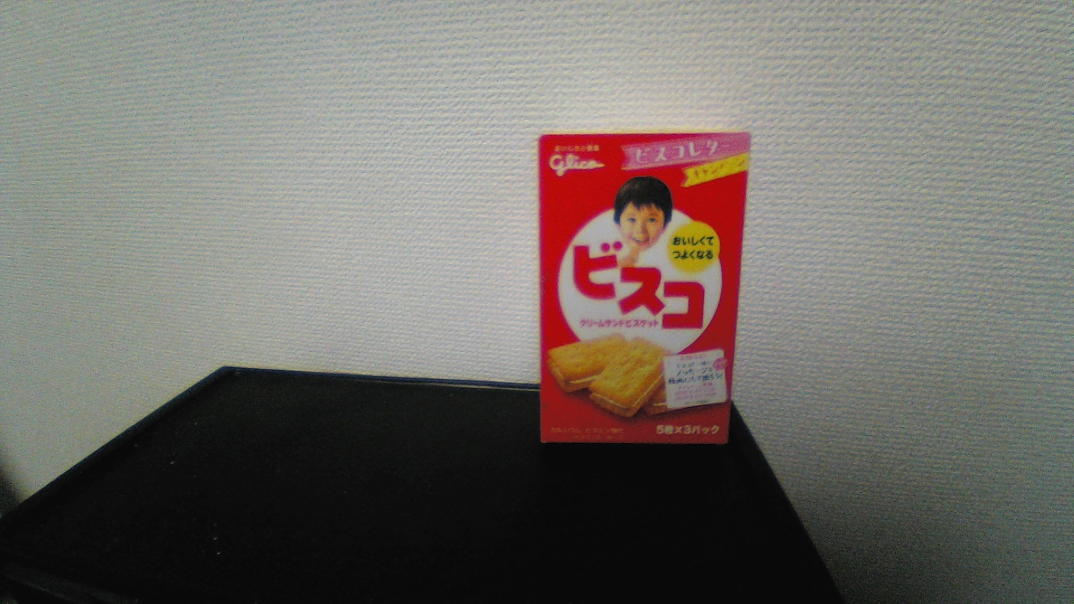
YOLO/bisco/face_001.jpg
