HidetoNiwa/one-person-catch-robo/YOLO/bisco/face_002.jpg

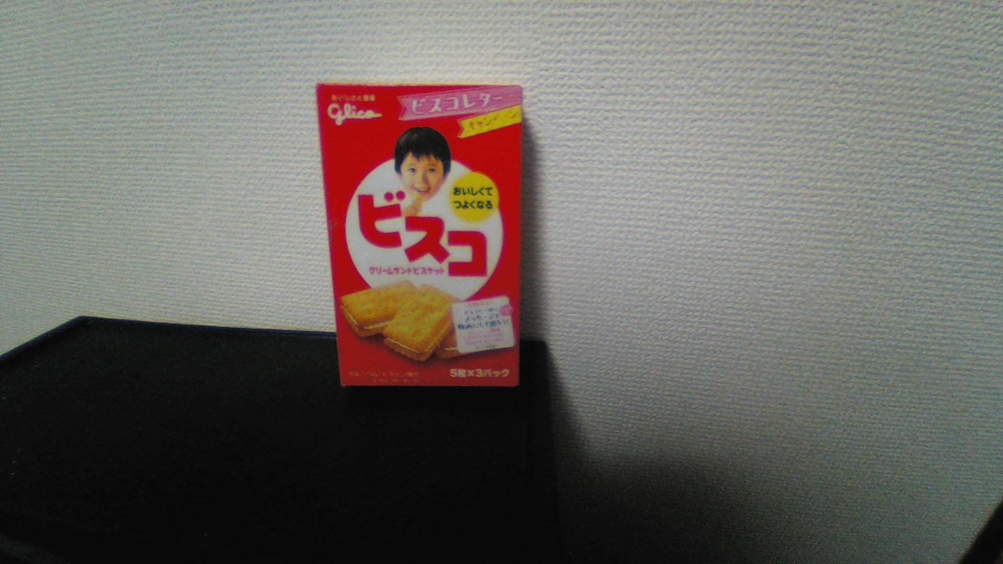
YOLO/bisco/face_002.jpg
