HidetoNiwa/one-person-catch-robo/YOLO/bisco/face_003.jpg

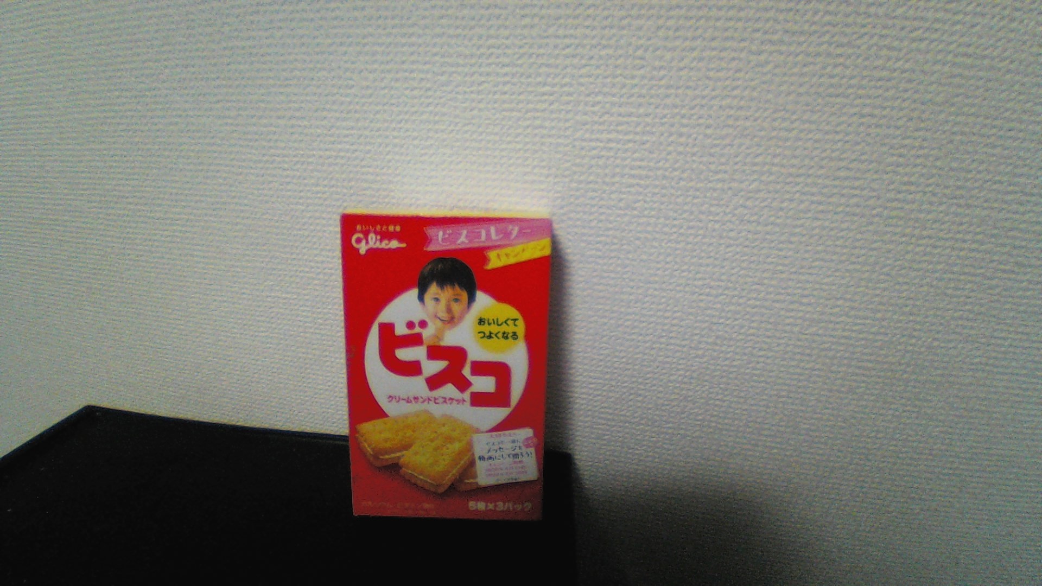
YOLO/bisco/face_003.jpg
