HidetoNiwa/one-person-catch-robo/YOLO/bisco/face_004.jpg

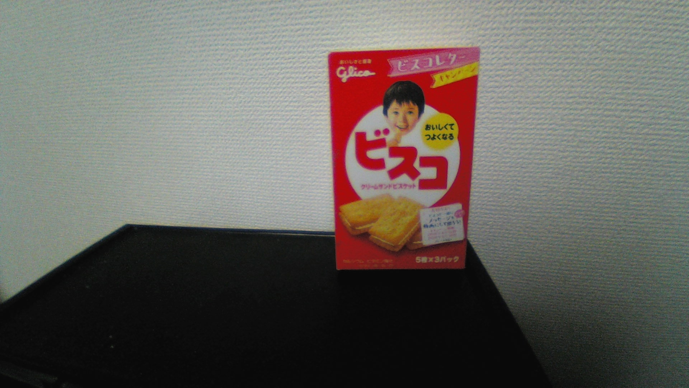
YOLO/bisco/face_004.jpg
