HidetoNiwa/one-person-catch-robo/YOLO/bisco/face_005.jpg

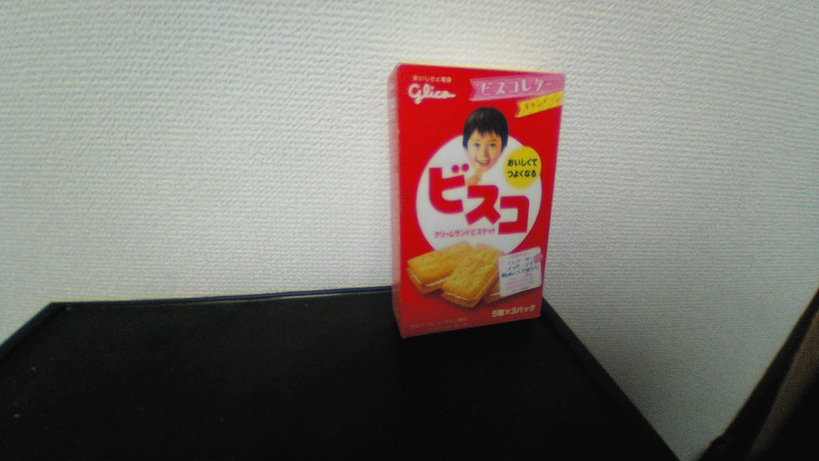
YOLO/bisco/face_005.jpg
