HidetoNiwa/one-person-catch-robo/YOLO/bisco/face_006.jpg

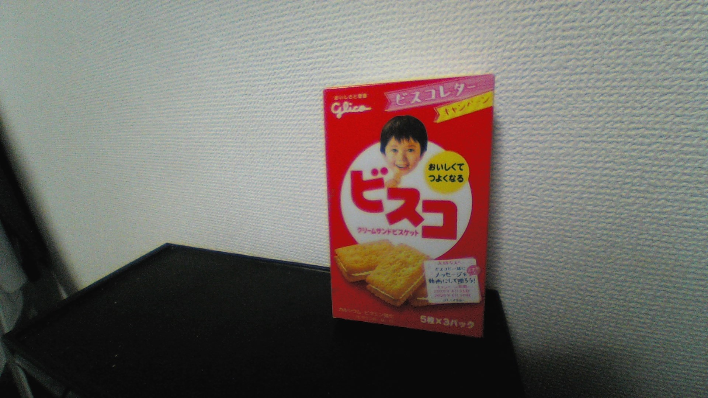
YOLO/bisco/face_006.jpg
