HidetoNiwa/one-person-catch-robo/YOLO/bisco/face_007.jpg

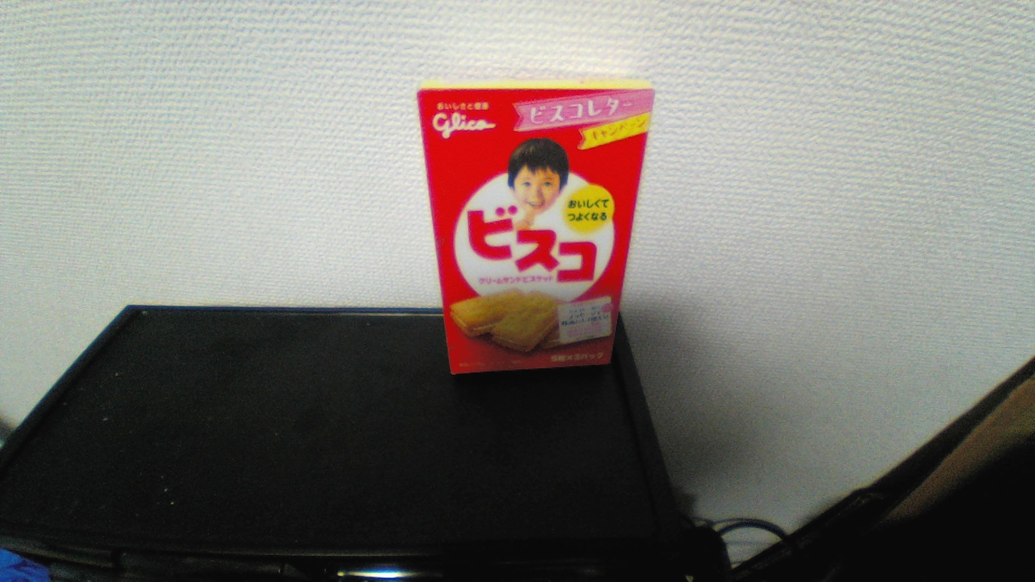
YOLO/bisco/face_007.jpg
