HidetoNiwa/one-person-catch-robo/YOLO/bisco/face_008.jpg

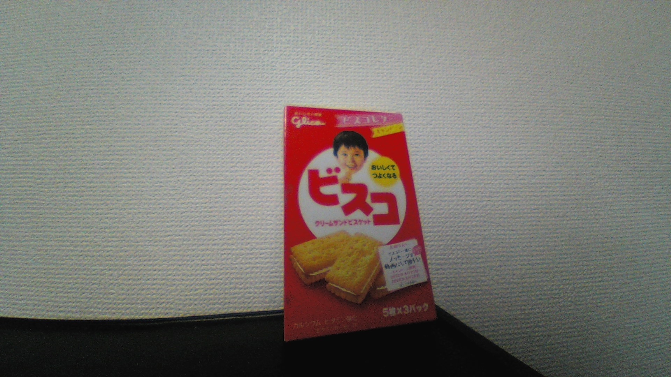
YOLO/bisco/face_008.jpg
