HidetoNiwa/one-person-catch-robo/YOLO/bisco/face_009.jpg

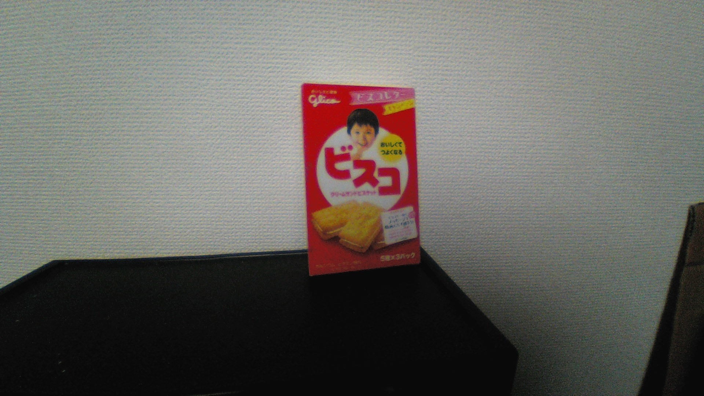
YOLO/bisco/face_009.jpg
