HidetoNiwa/one-person-catch-robo/YOLO/bisco/face_010.jpg

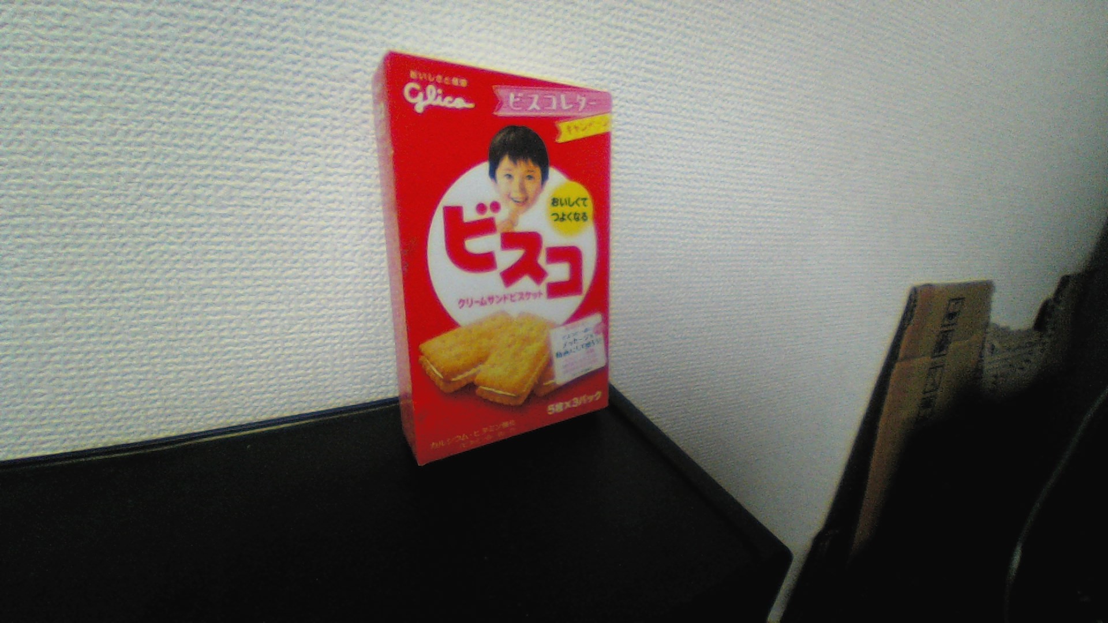
YOLO/bisco/face_010.jpg
