HidetoNiwa/one-person-catch-robo/YOLO/bisco/face_011.jpg

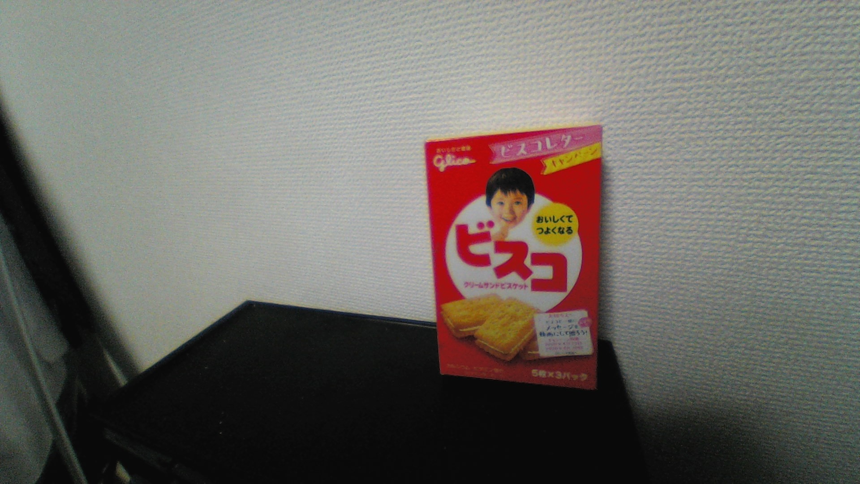
YOLO/bisco/face_011.jpg
