HidetoNiwa/one-person-catch-robo/YOLO/bisco/face_012.jpg

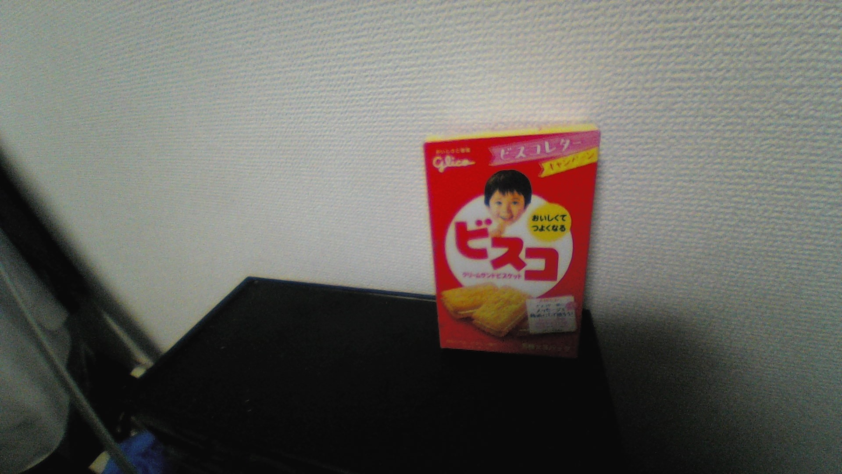
YOLO/bisco/face_012.jpg
