HidetoNiwa/one-person-catch-robo/YOLO/bisco/face_013.jpg

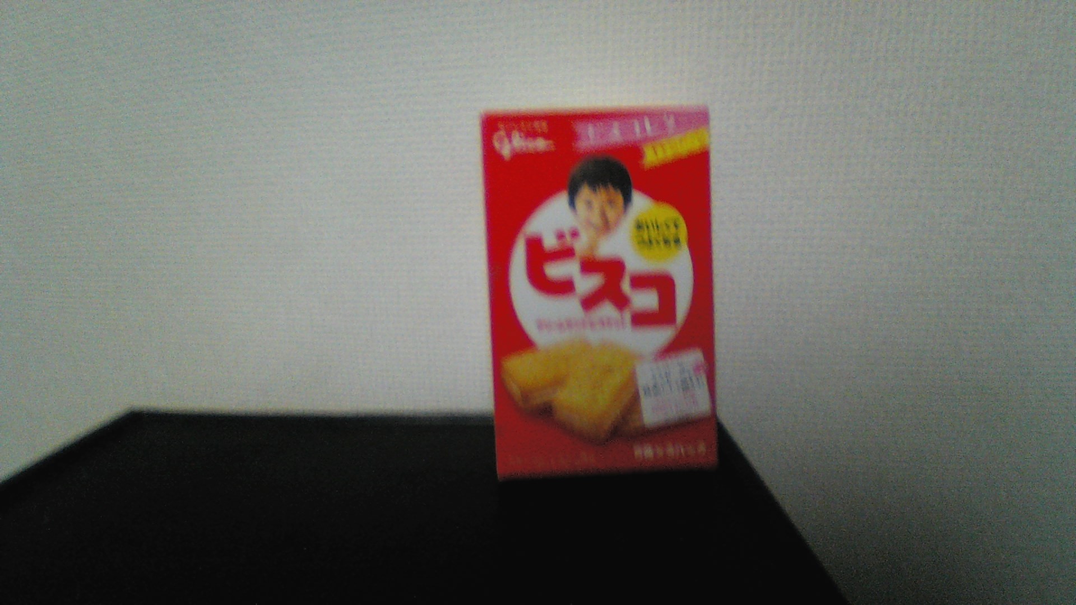
YOLO/bisco/face_013.jpg
