HidetoNiwa/one-person-catch-robo/YOLO/bisco/face_014.jpg

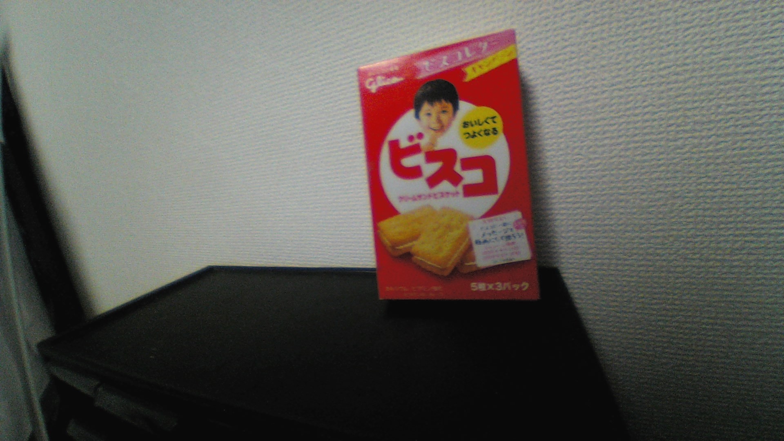
YOLO/bisco/face_014.jpg
