HidetoNiwa/one-person-catch-robo/YOLO/bisco/face_015.jpg

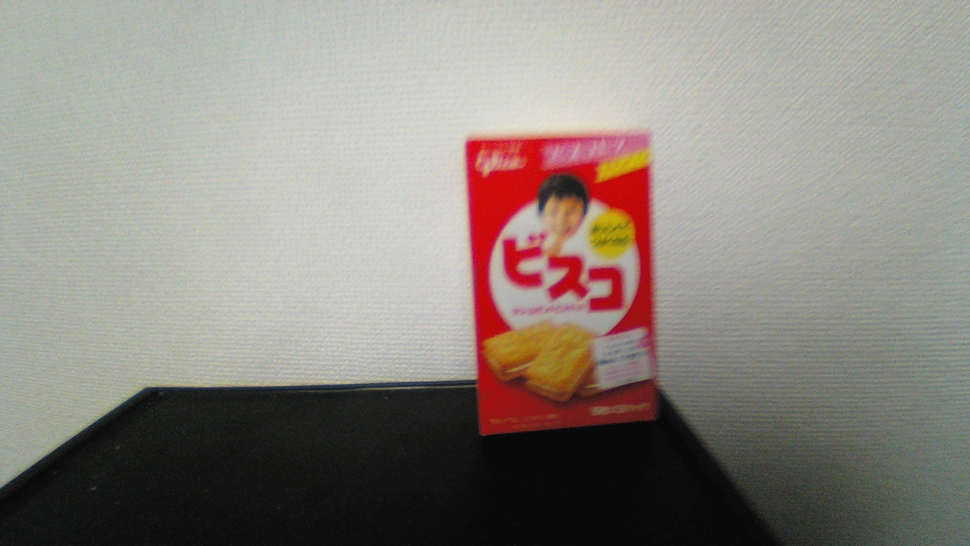
YOLO/bisco/face_015.jpg
