HidetoNiwa/one-person-catch-robo/YOLO/bisco/face_017.jpg

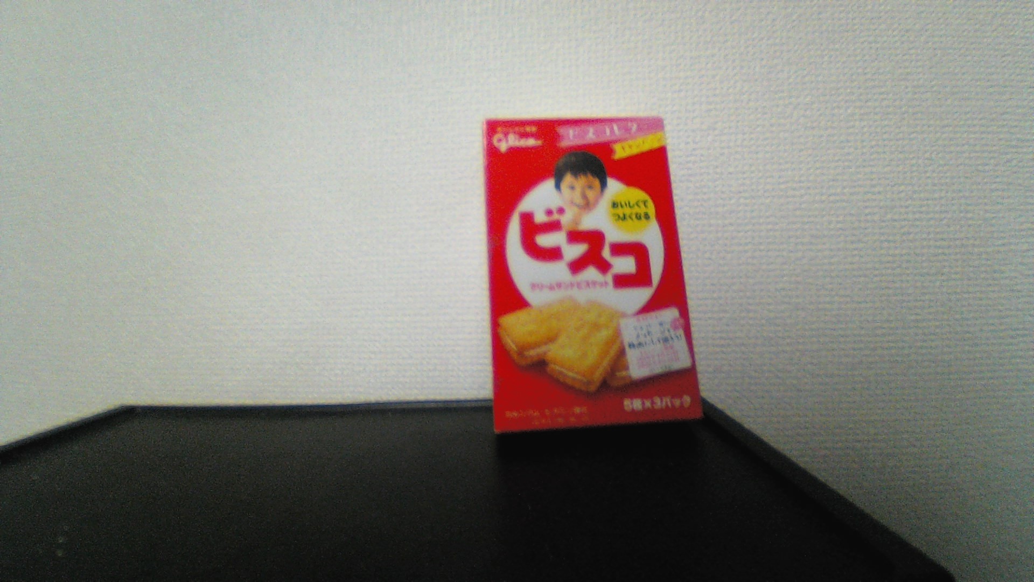
YOLO/bisco/face_017.jpg
