HidetoNiwa/one-person-catch-robo/YOLO/bisco/face_019.jpg

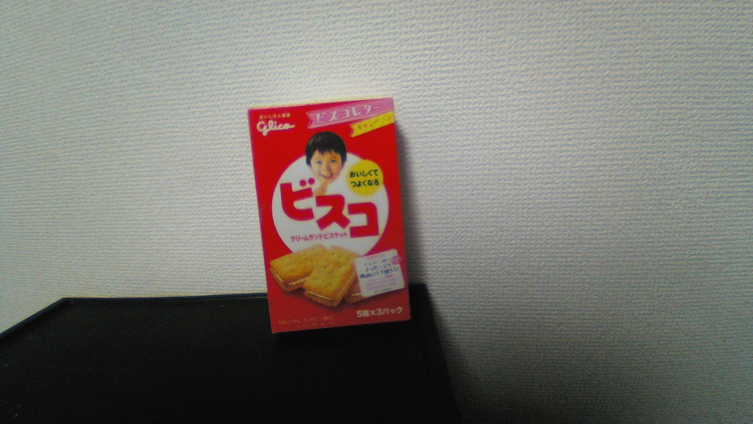
YOLO/bisco/face_019.jpg
