HidetoNiwa/one-person-catch-robo/YOLO/bisco/face_020.jpg

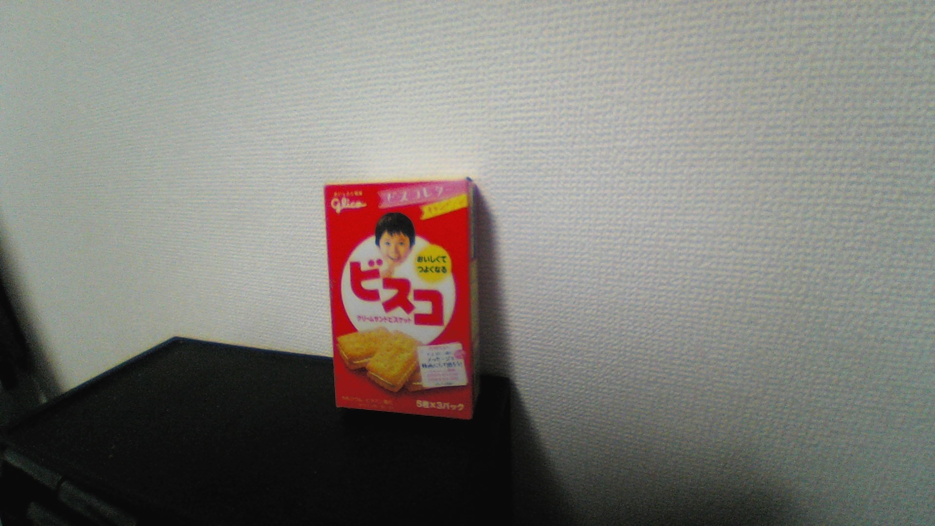
YOLO/bisco/face_020.jpg
