HidetoNiwa/one-person-catch-robo/YOLO/bisco/face_021.jpg

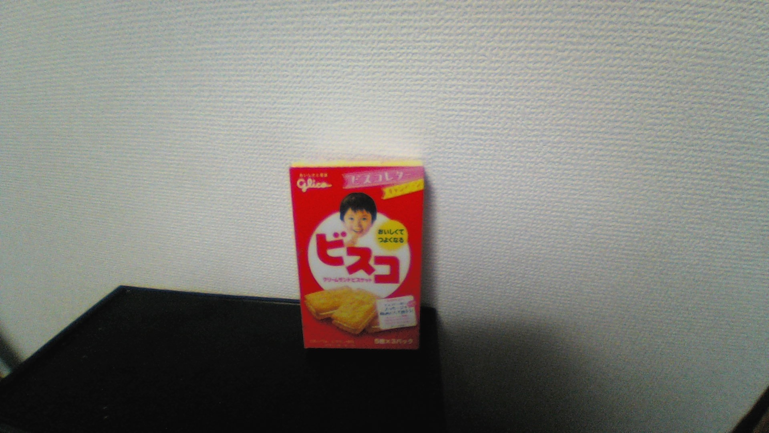
YOLO/bisco/face_021.jpg
