HidetoNiwa/one-person-catch-robo/YOLO/bisco/face_022.jpg

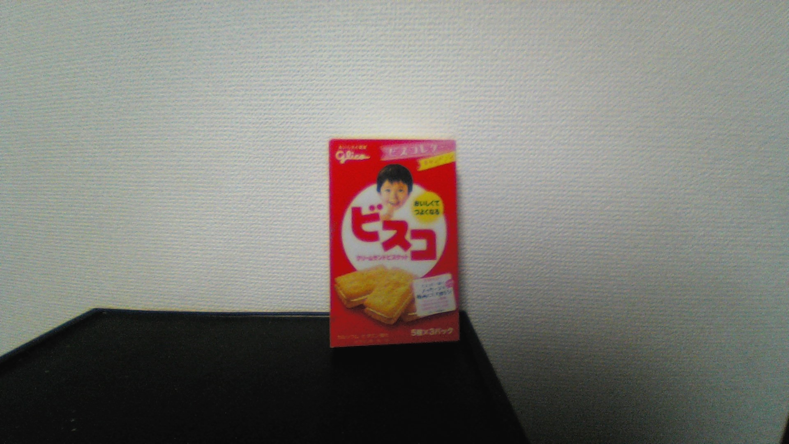
YOLO/bisco/face_022.jpg
