HidetoNiwa/one-person-catch-robo/YOLO/bisco/face_023.jpg

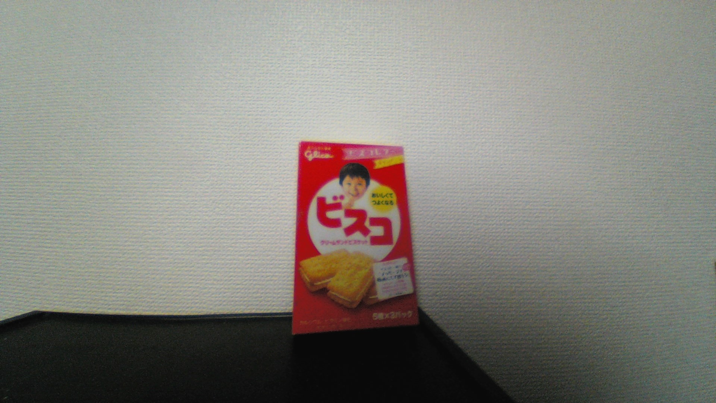
YOLO/bisco/face_023.jpg
