HidetoNiwa/one-person-catch-robo/YOLO/bisco/face_024.jpg

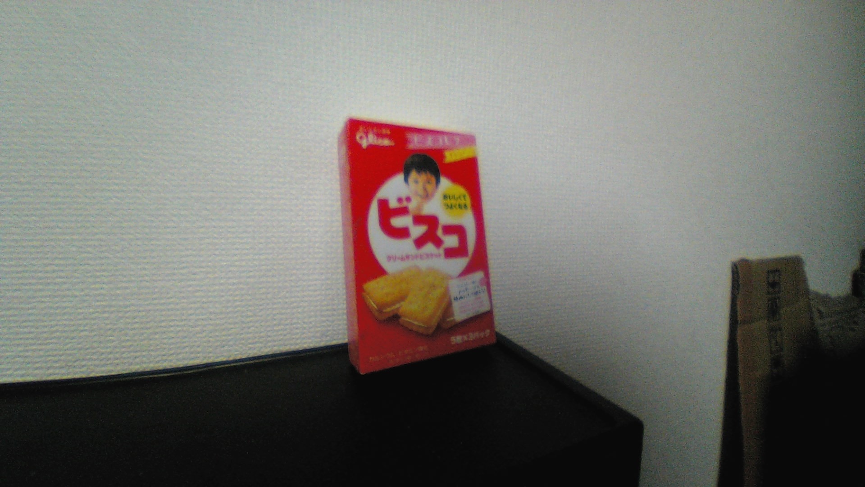
YOLO/bisco/face_024.jpg
