HidetoNiwa/one-person-catch-robo/YOLO/bisco/face_025.jpg

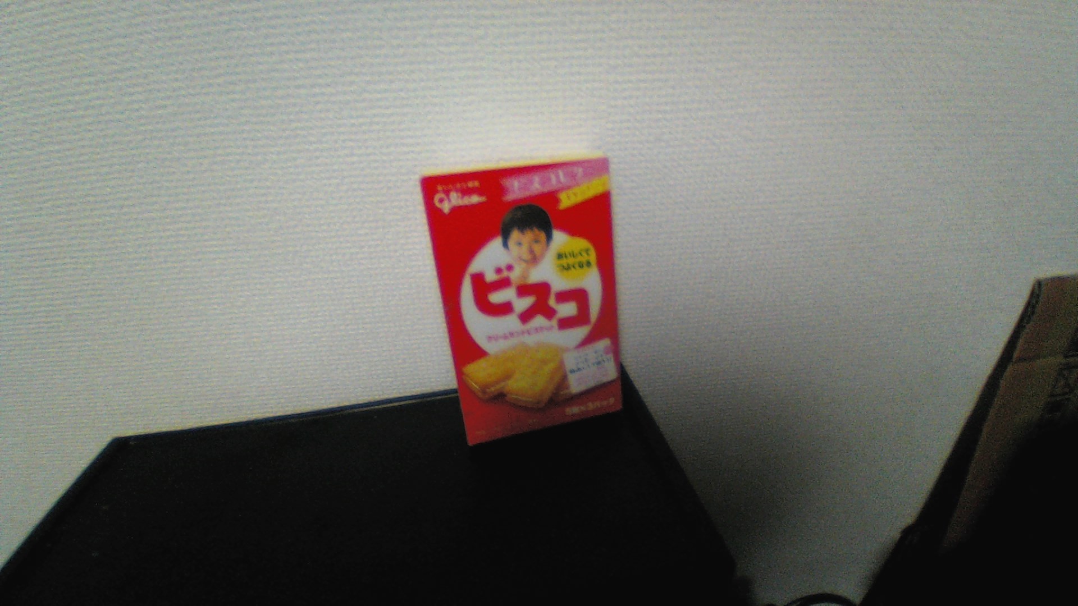
YOLO/bisco/face_025.jpg
