HidetoNiwa/one-person-catch-robo/YOLO/bisco/face_026.jpg

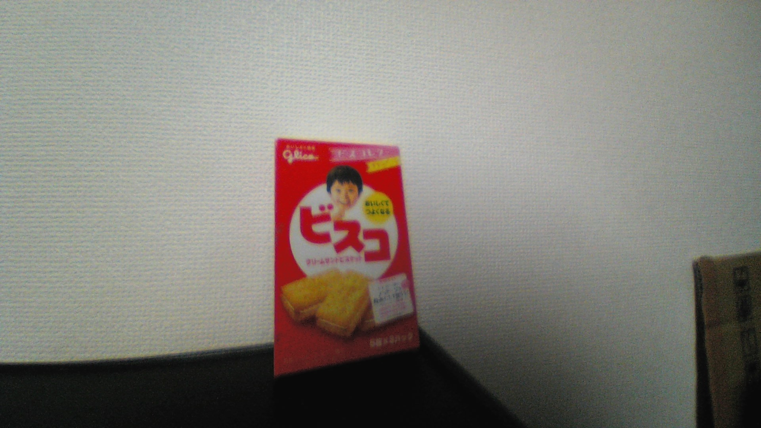
YOLO/bisco/face_026.jpg
