HidetoNiwa/one-person-catch-robo/YOLO/bisco/face_028.jpg

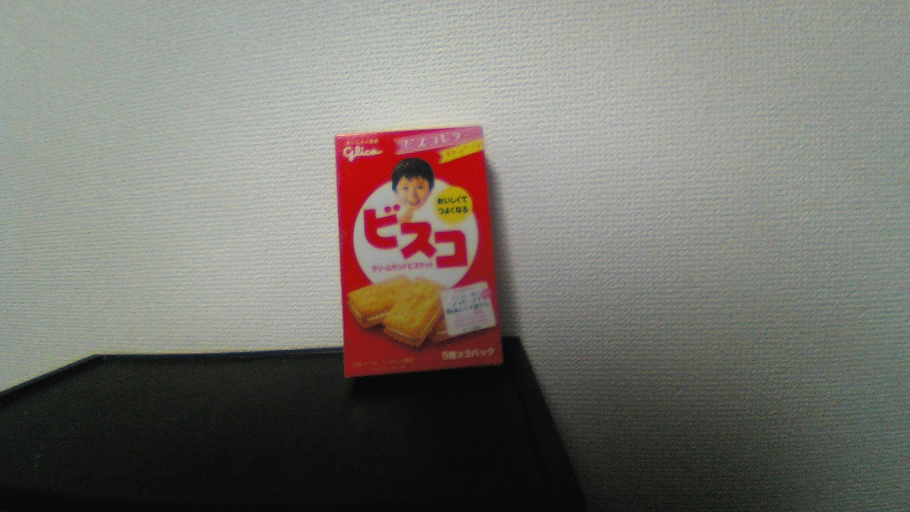
YOLO/bisco/face_028.jpg
