HidetoNiwa/one-person-catch-robo/YOLO/bisco/face_029.jpg

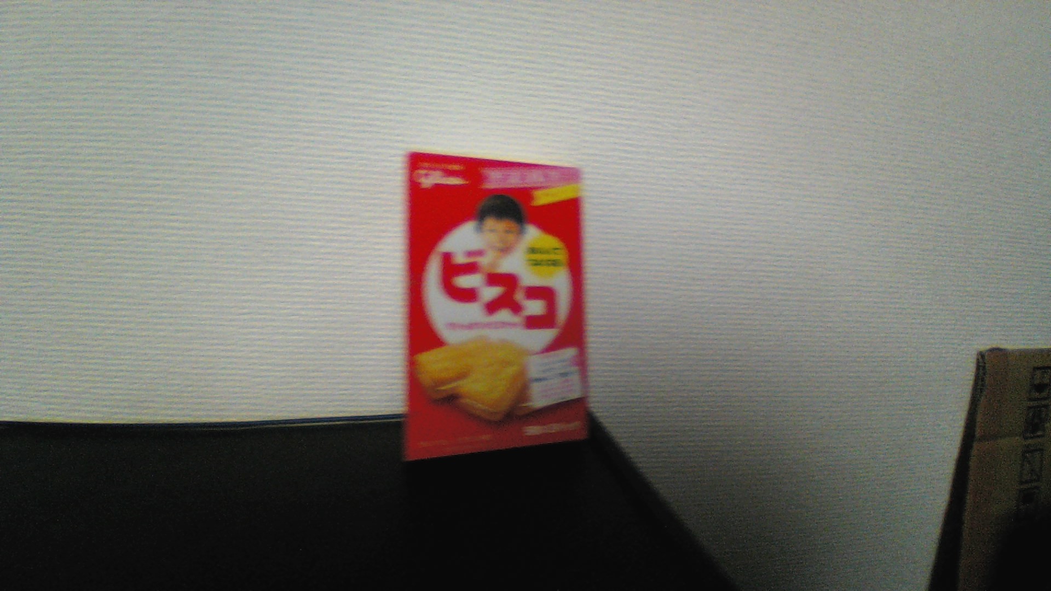
YOLO/bisco/face_029.jpg
