HidetoNiwa/one-person-catch-robo/YOLO/bisco/face_031.jpg

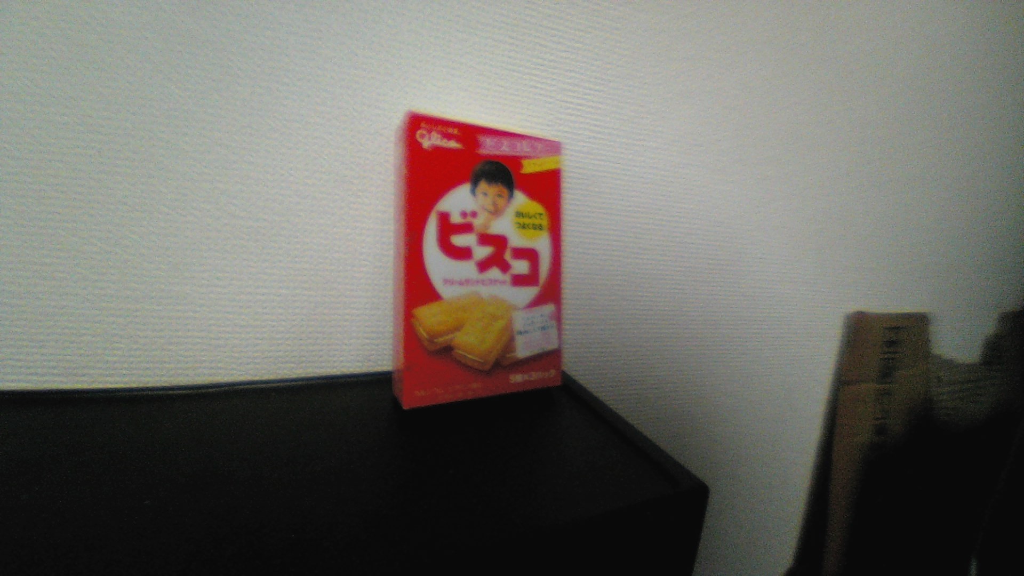
YOLO/bisco/face_031.jpg
