HidetoNiwa/one-person-catch-robo/YOLO/bisco/face_032.jpg

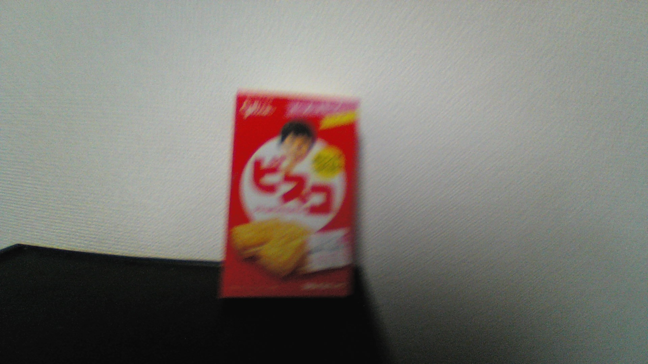
YOLO/bisco/face_032.jpg
