HidetoNiwa/one-person-catch-robo/YOLO/bisco/face_034.jpg

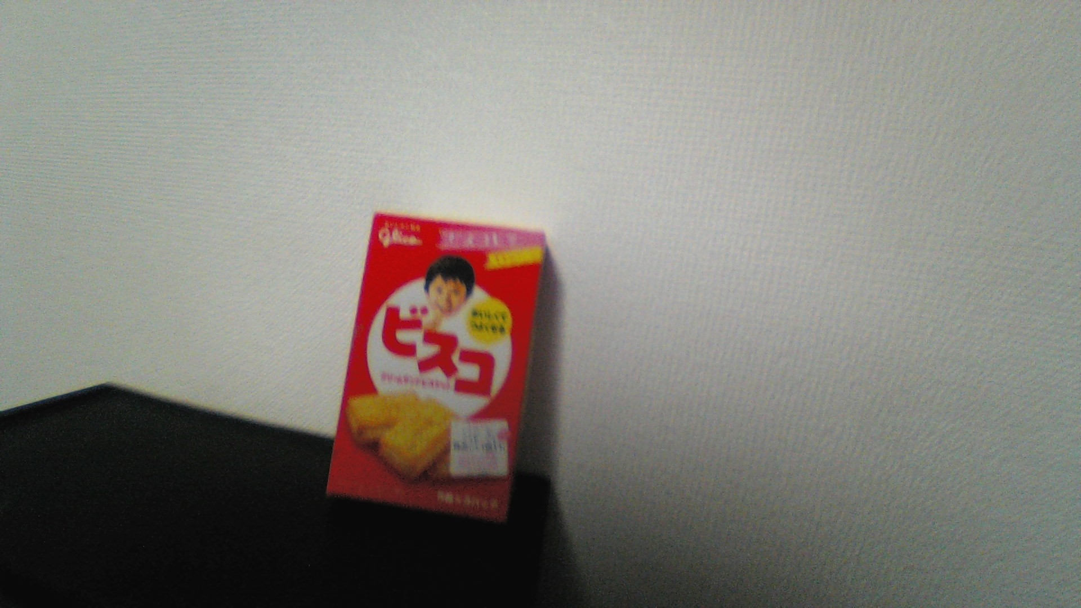
YOLO/bisco/face_034.jpg
