HidetoNiwa/one-person-catch-robo/YOLO/bisco/face_036.jpg

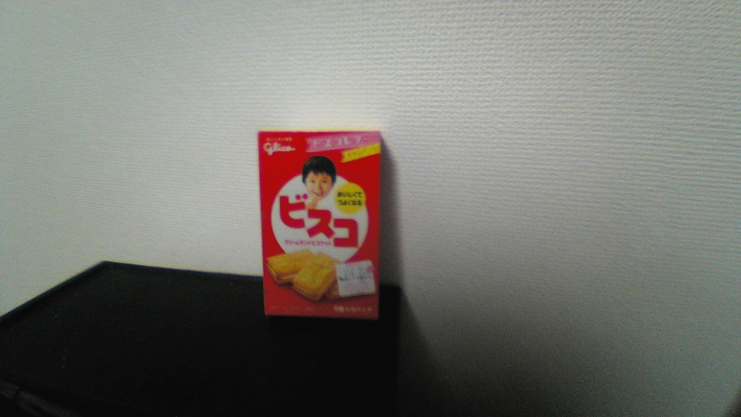
YOLO/bisco/face_036.jpg
