HidetoNiwa/one-person-catch-robo/YOLO/bisco/face_037.jpg

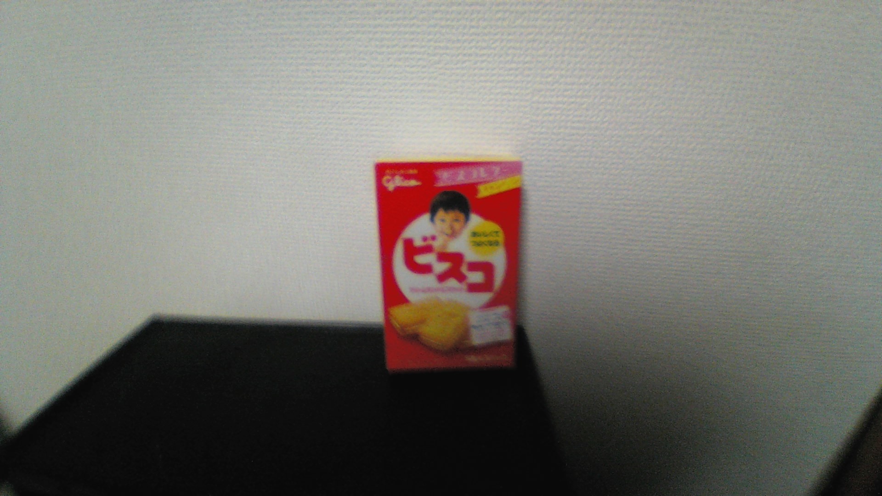
YOLO/bisco/face_037.jpg
