HidetoNiwa/one-person-catch-robo/YOLO/bisco/face_038.jpg

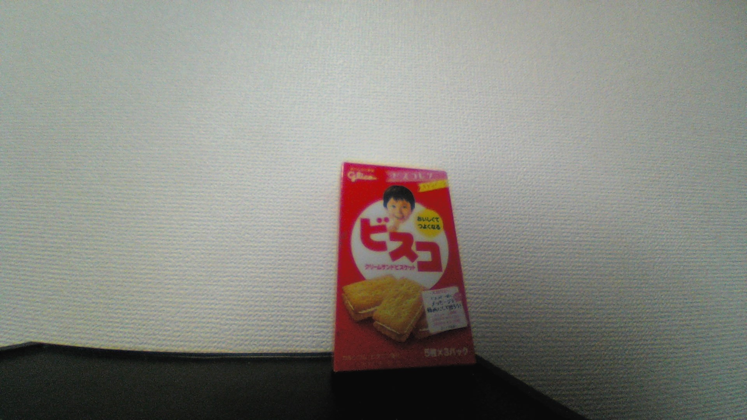
YOLO/bisco/face_038.jpg
