HidetoNiwa/one-person-catch-robo/提出資料/紹介ビデオ/sozai/DSC_0025.JPG

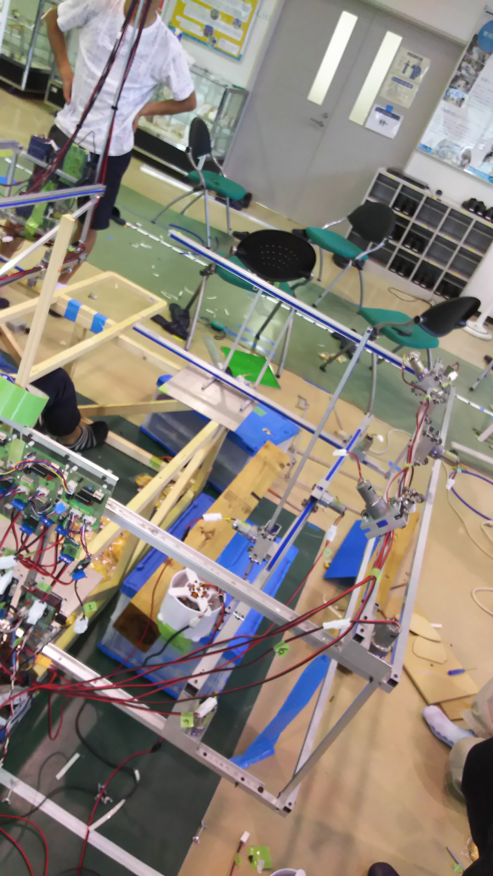
提出資料/紹介ビデオ/sozai/DSC_0025.JPG
