HidetoNiwa/one-person-catch-robo/提出資料/紹介ビデオ/sozai/DSC_0126.jpg

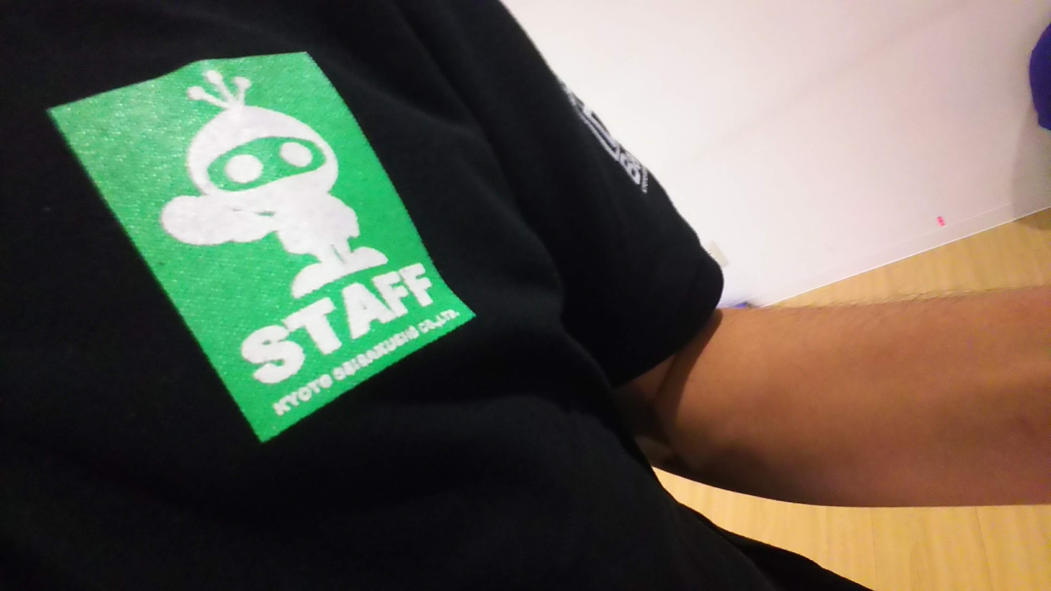
提出資料/紹介ビデオ/sozai/DSC_0126.jpg
