HidetoNiwa/one-person-catch-robo/提出資料/紹介ビデオ/sozai/DSC_0428.JPG

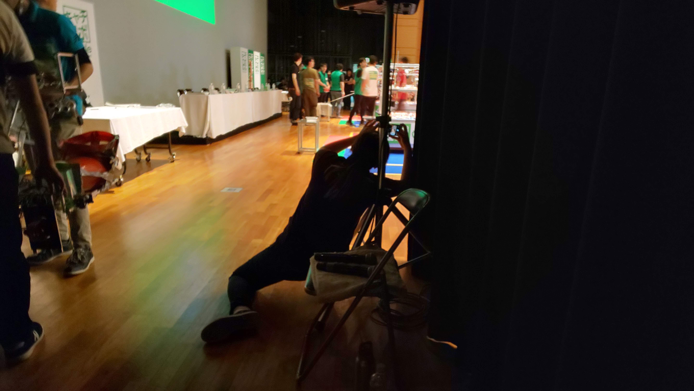
提出資料/紹介ビデオ/sozai/DSC_0428.JPG
