HidetoNiwa/one-person-catch-robo/提出資料/紹介ビデオ/sozai/IMG_20170911_231419_603.jpg

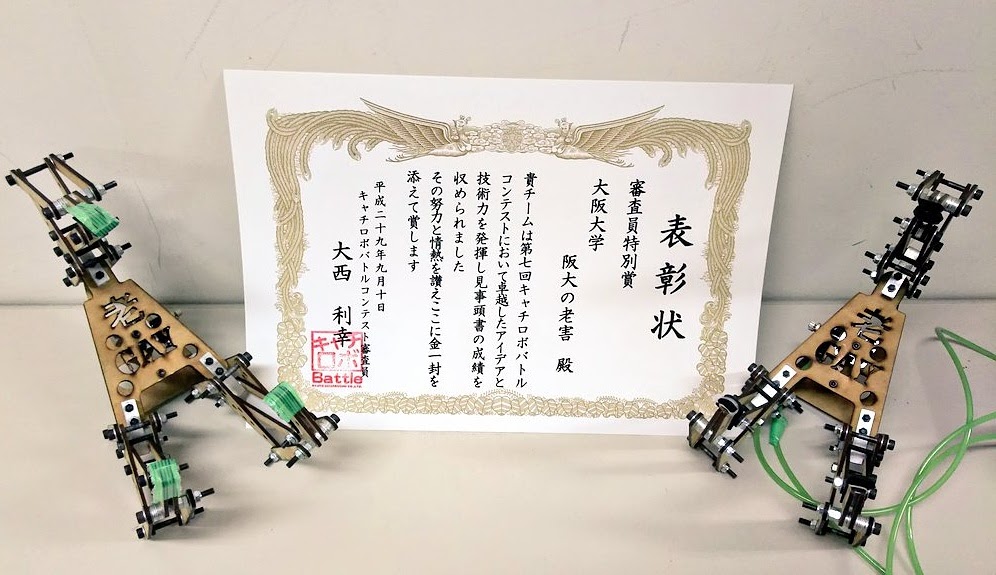
提出資料/紹介ビデオ/sozai/IMG_20170911_231419_603.jpg
