HidetoNiwa/one-person-catch-robo/CAD/ロボット/Images/ロボット.iam 構造解析レポート 2020_07_17/0/Result_0_4_rev.png

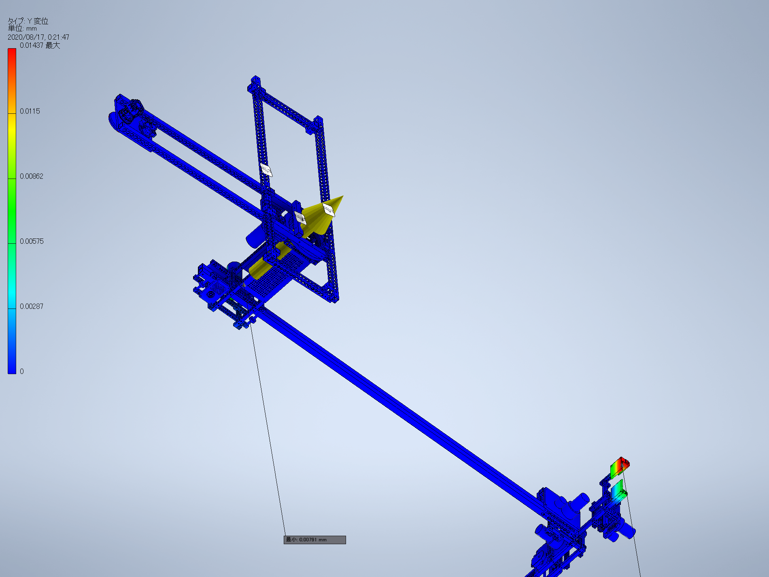
CAD/ロボット/Images/ロボット.iam 構造解析レポート 2020_07_17/0/Result_0_4_rev.png
